allisonmb/game-gear/A-Z80/docs/png/a-z80-toplevel.png

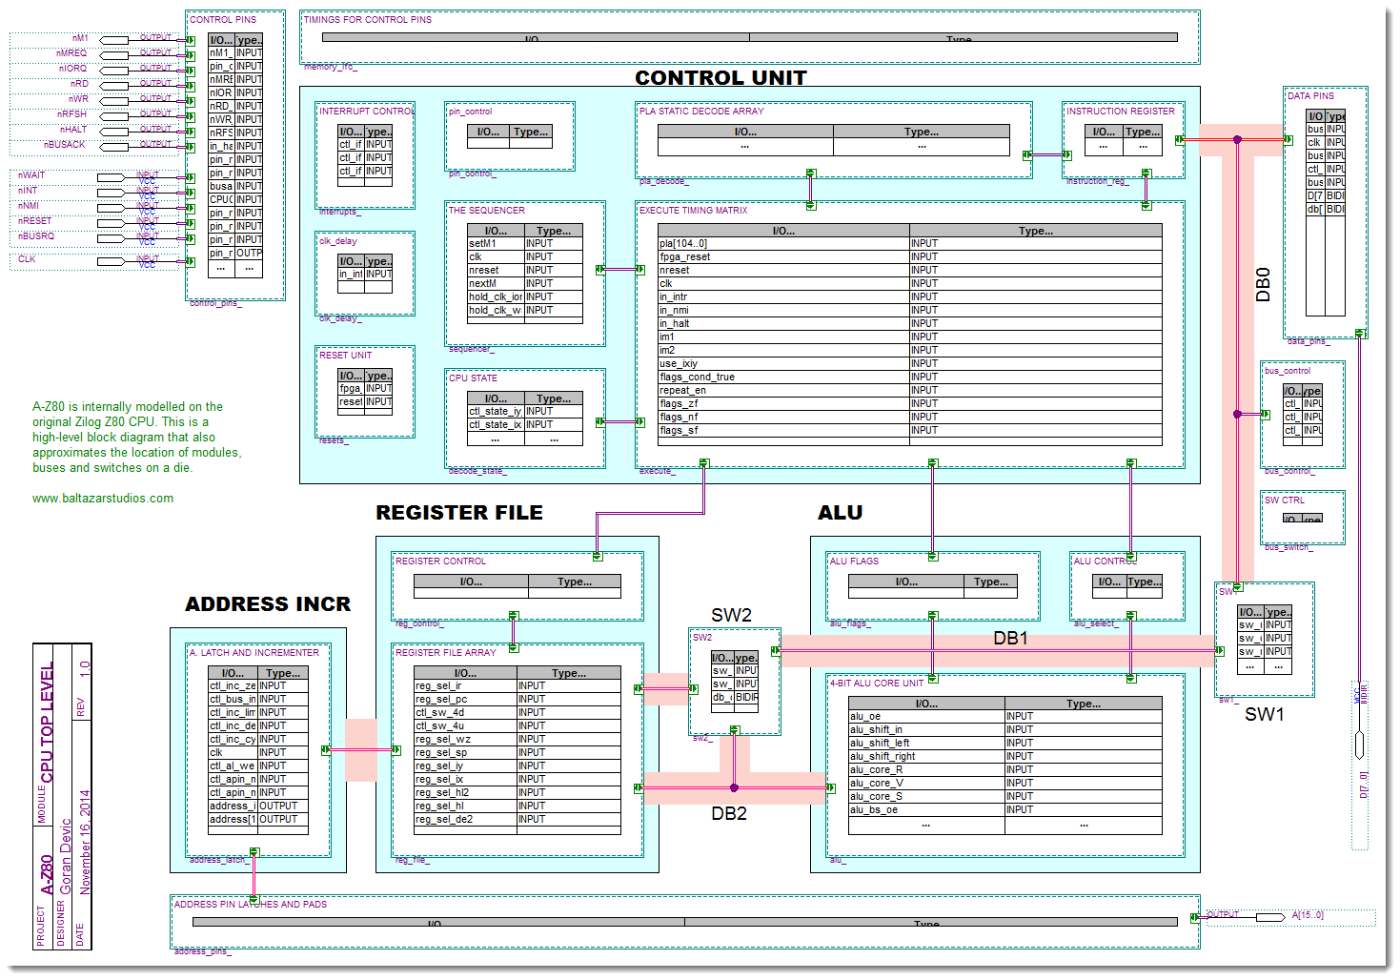
A-Z80/docs/png/a-z80-toplevel.png
