allisonmb/game-gear/A-Z80/docs/png/z80-address_pins.png

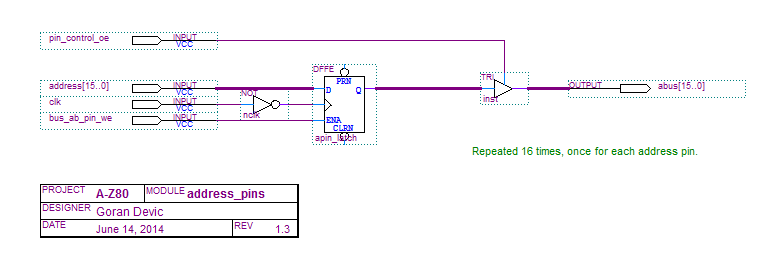
A-Z80/docs/png/z80-address_pins.png
