allisonmb/game-gear/A-Z80/docs/png/z80-alu.png

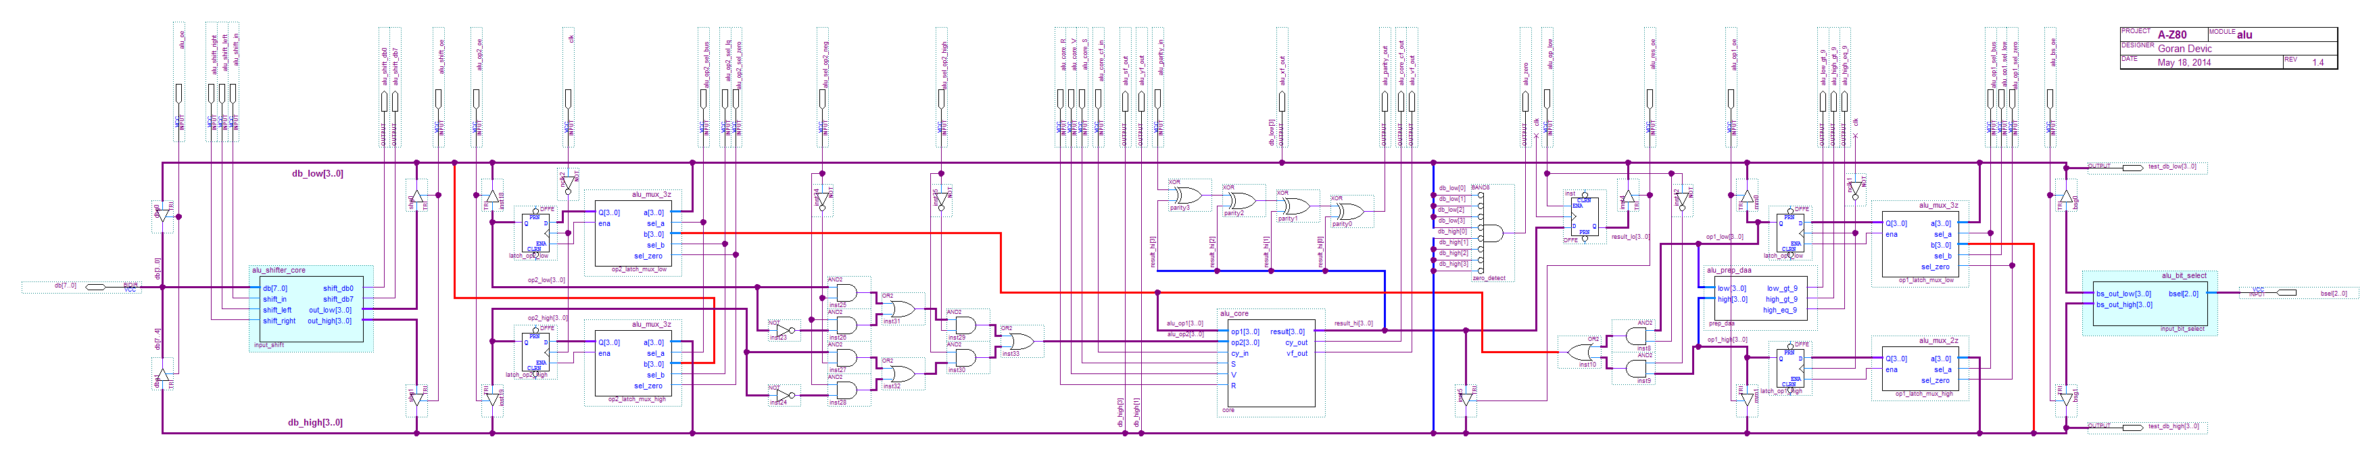
A-Z80/docs/png/z80-alu.png
