allisonmb/game-gear/A-Z80/docs/png/z80-alu_control.png

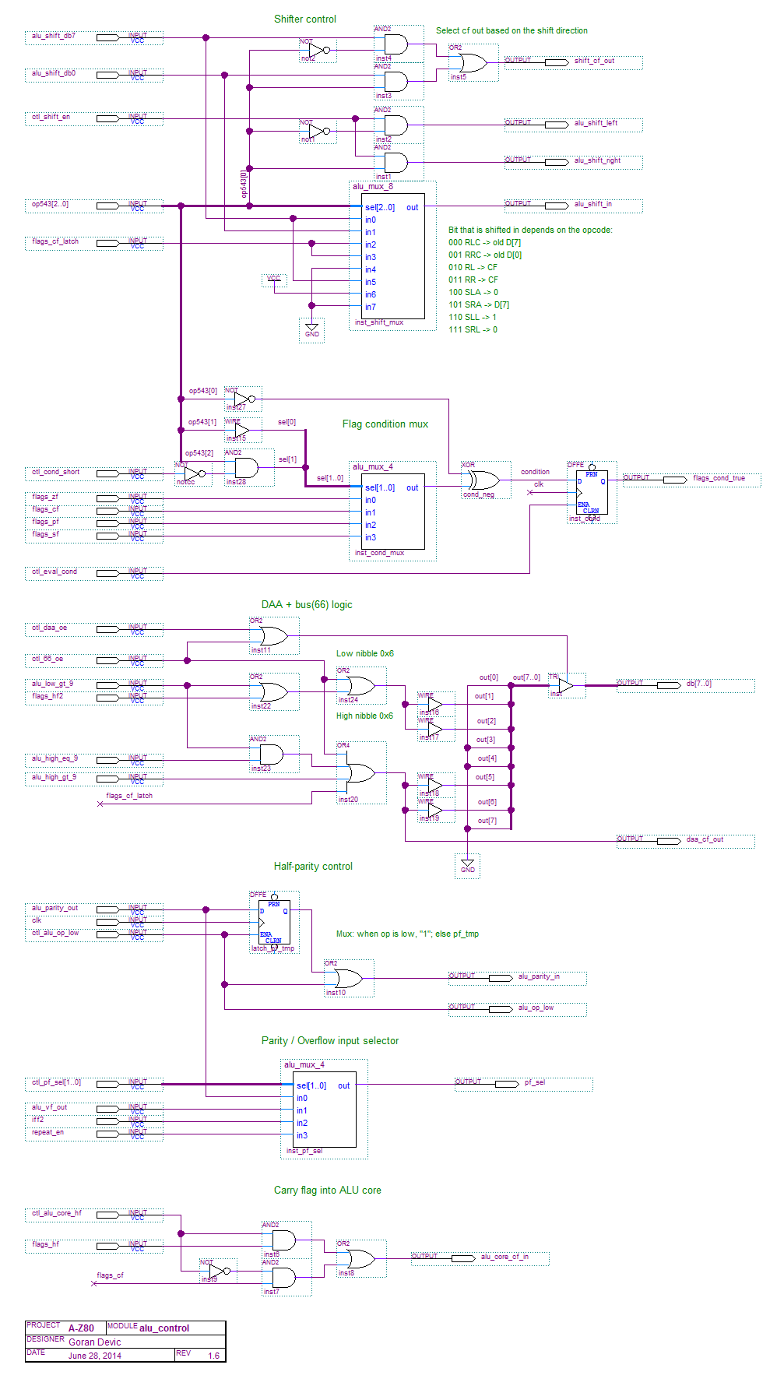
A-Z80/docs/png/z80-alu_control.png
