allisonmb/game-gear/A-Z80/docs/png/z80-alu_flags.png

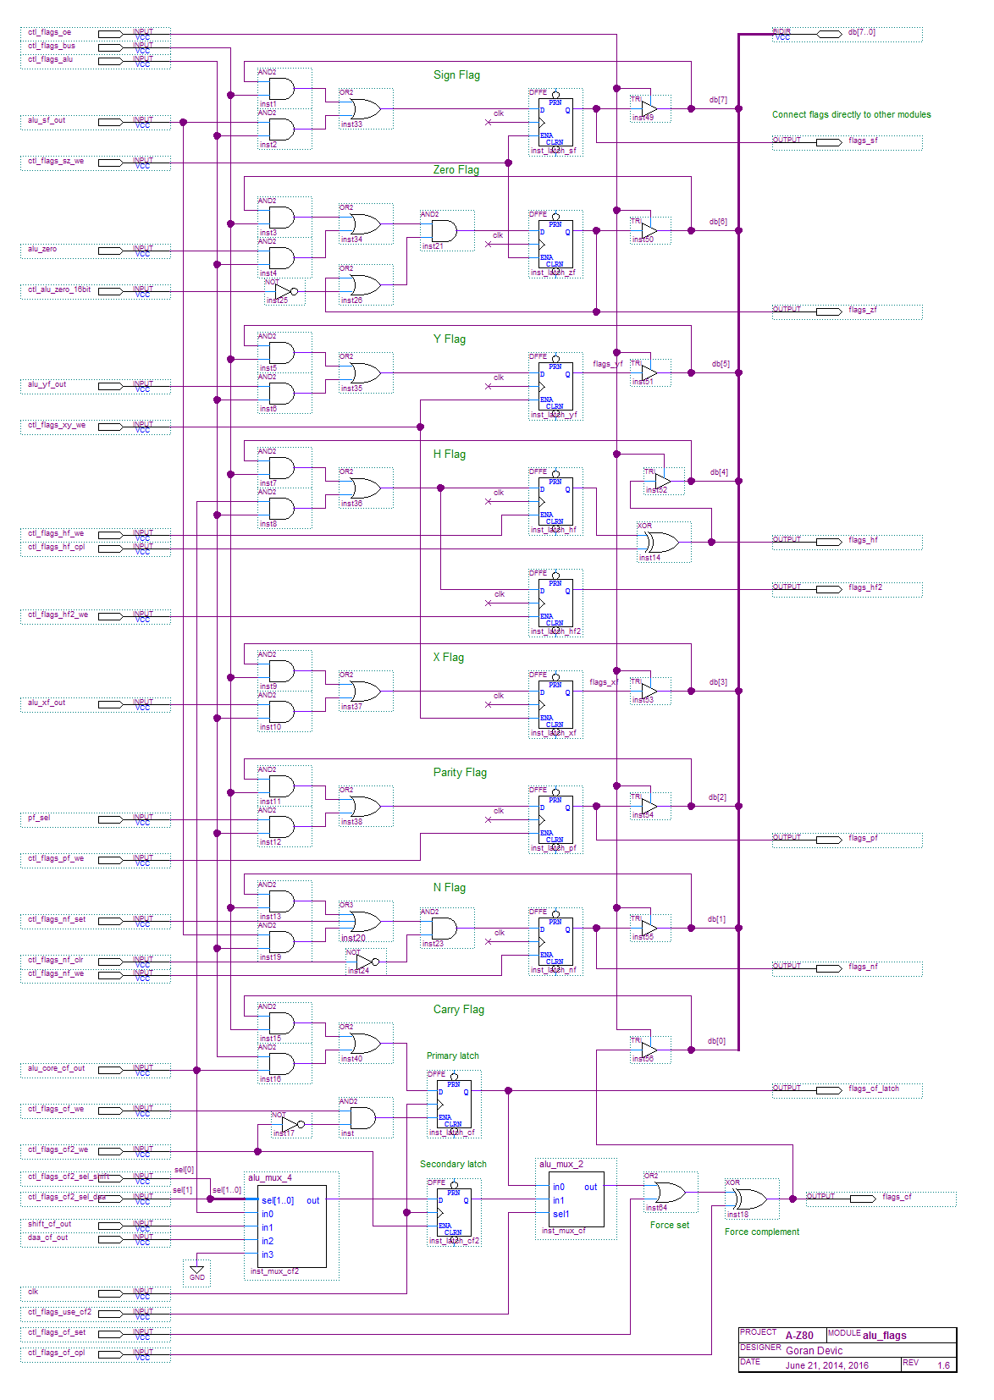
A-Z80/docs/png/z80-alu_flags.png
