allisonmb/game-gear/A-Z80/docs/png/z80-alu_mux_2z.png

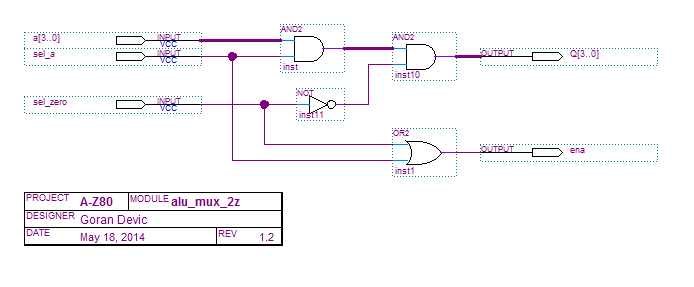
A-Z80/docs/png/z80-alu_mux_2z.png
