allisonmb/game-gear/A-Z80/docs/png/z80-alu_mux_4.png

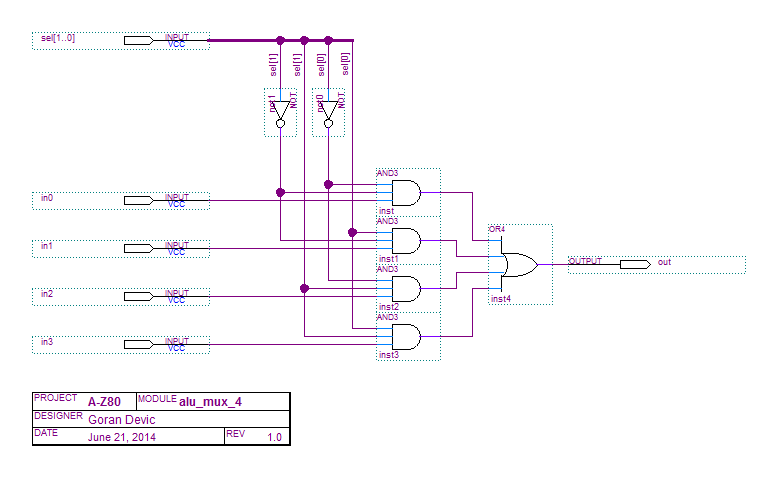
A-Z80/docs/png/z80-alu_mux_4.png
