allisonmb/game-gear/A-Z80/docs/png/z80-alu_prep_daa.png

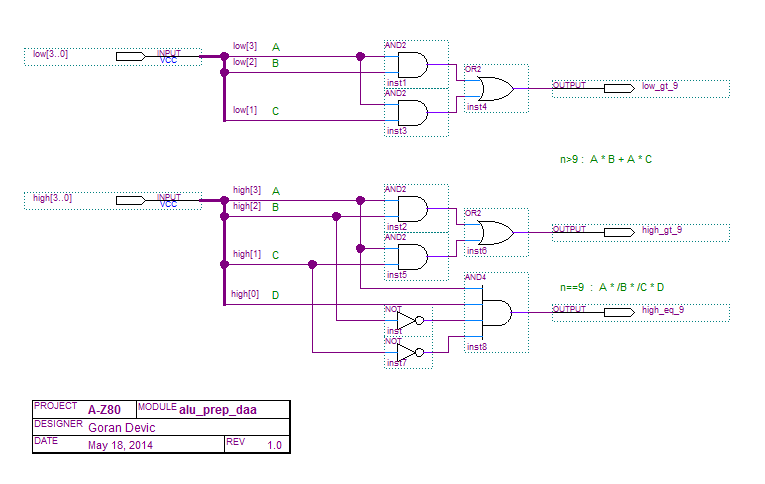
A-Z80/docs/png/z80-alu_prep_daa.png
