allisonmb/game-gear/A-Z80/docs/png/z80-alu_select.png

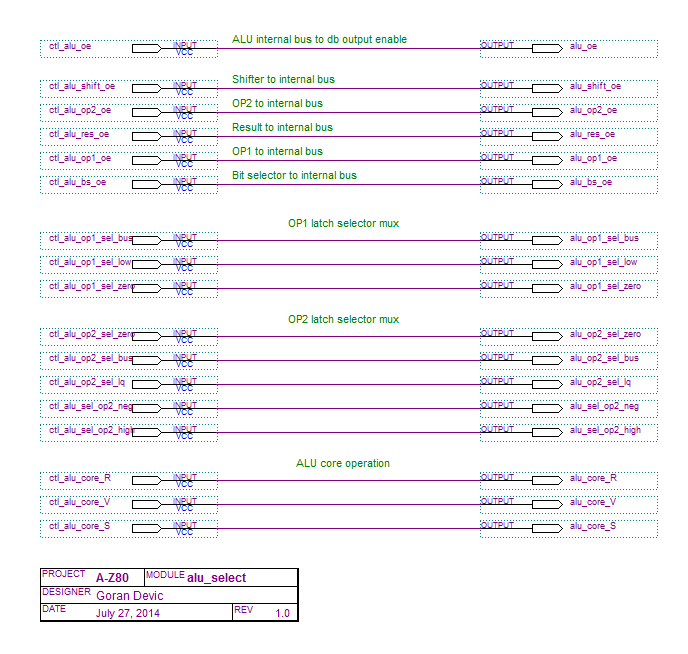
A-Z80/docs/png/z80-alu_select.png
