allisonmb/game-gear/A-Z80/docs/png/z80-clk_delay.png

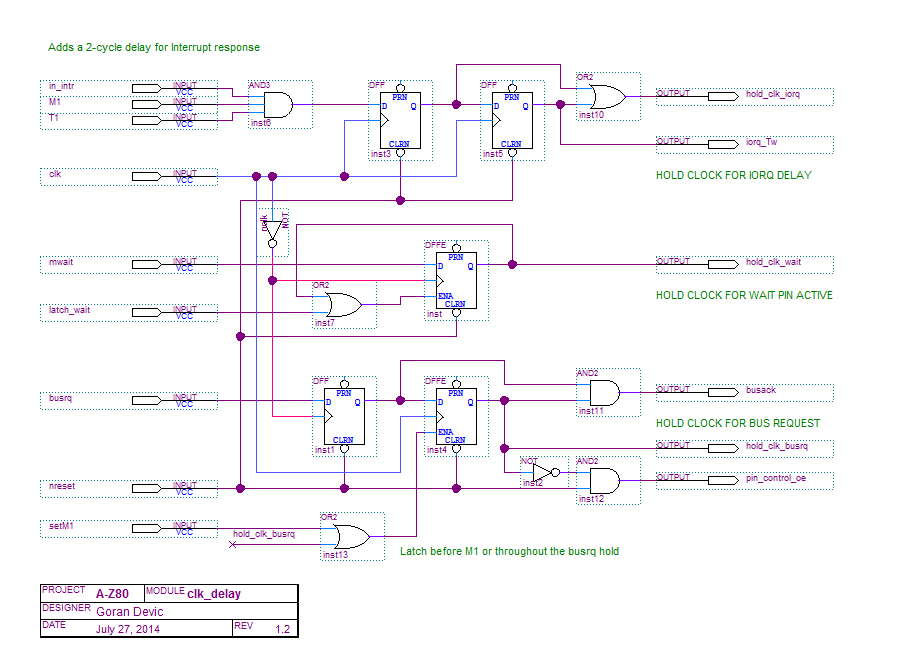
A-Z80/docs/png/z80-clk_delay.png
