allisonmb/game-gear/A-Z80/docs/png/z80-control_pins_n.png

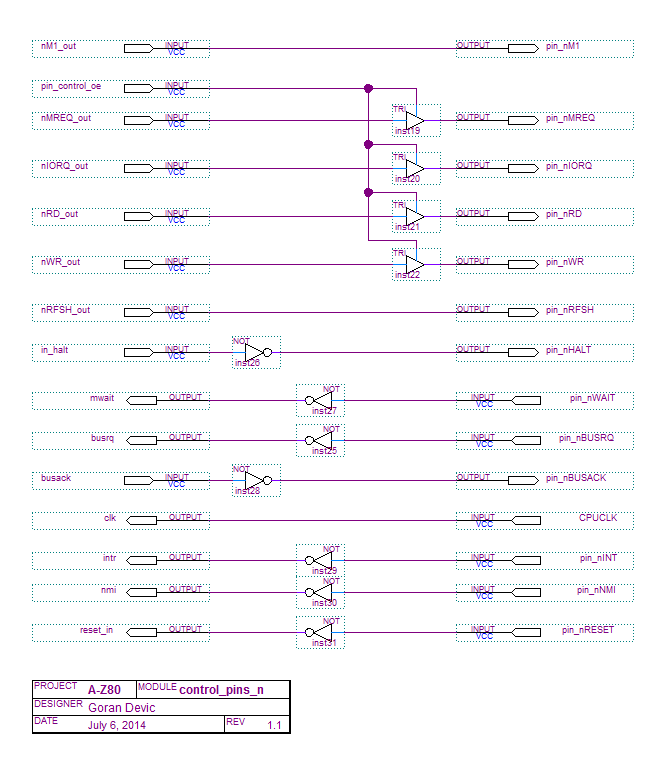
A-Z80/docs/png/z80-control_pins_n.png
