allisonmb/game-gear/A-Z80/docs/png/z80-data_pins.png

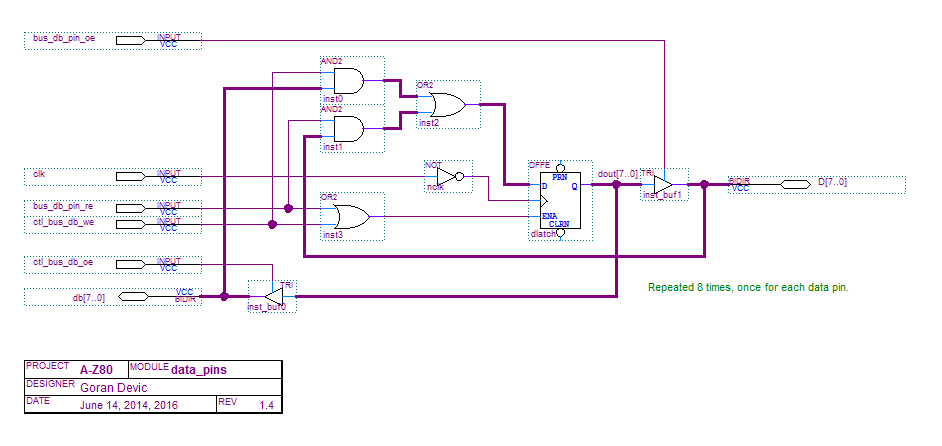
A-Z80/docs/png/z80-data_pins.png
