allisonmb/game-gear/A-Z80/docs/png/z80-data_switch.png

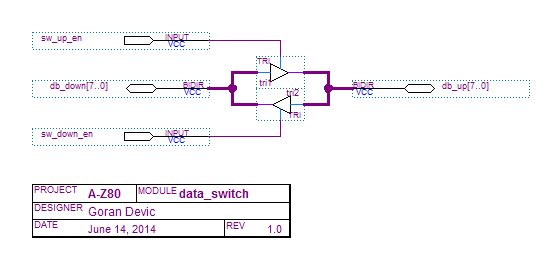
A-Z80/docs/png/z80-data_switch.png
