allisonmb/game-gear/A-Z80/docs/png/z80-data_switch_mask.png

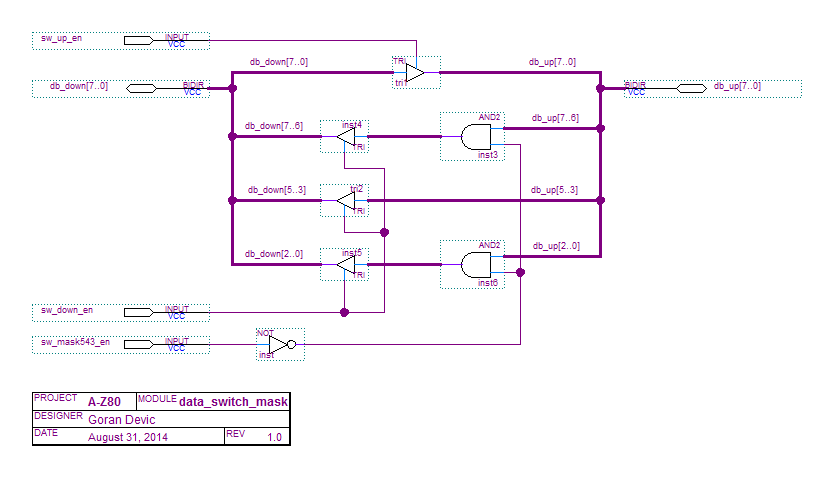
A-Z80/docs/png/z80-data_switch_mask.png
