allisonmb/game-gear/A-Z80/docs/png/z80-decode_state.png

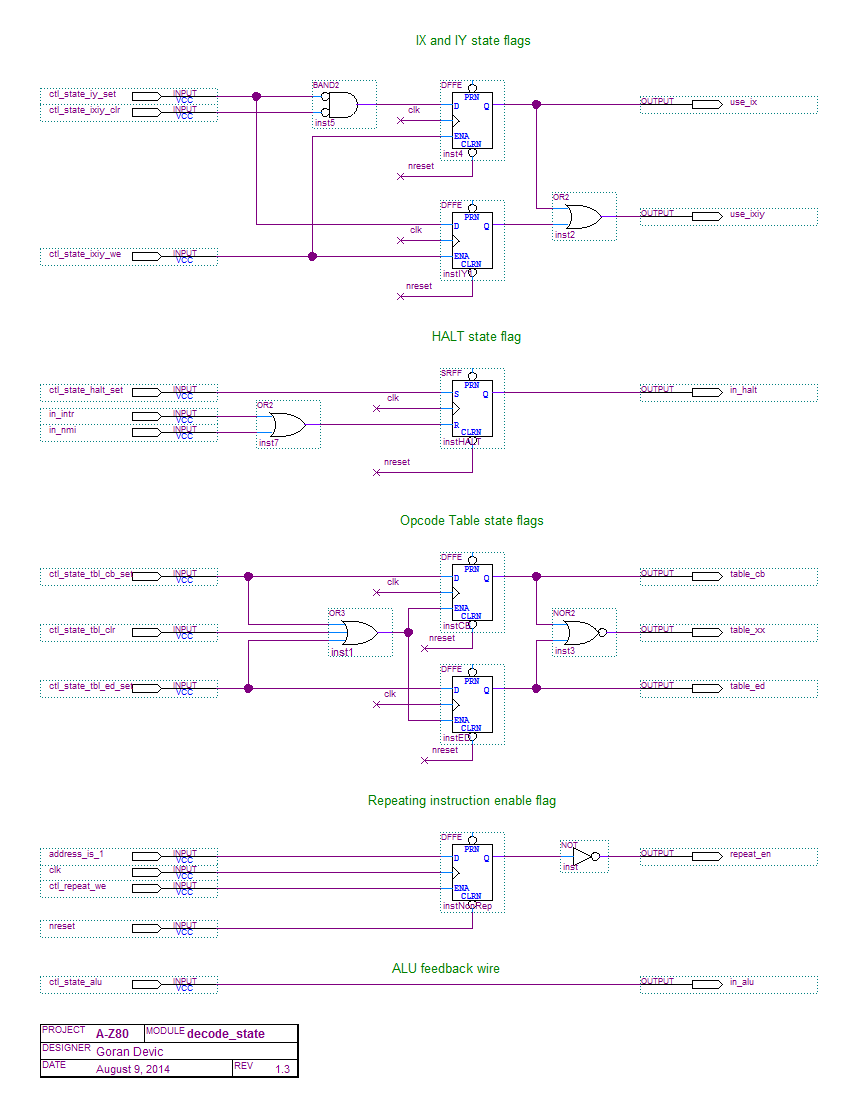
A-Z80/docs/png/z80-decode_state.png
