allisonmb/game-gear/A-Z80/docs/png/z80-inc_dec.png

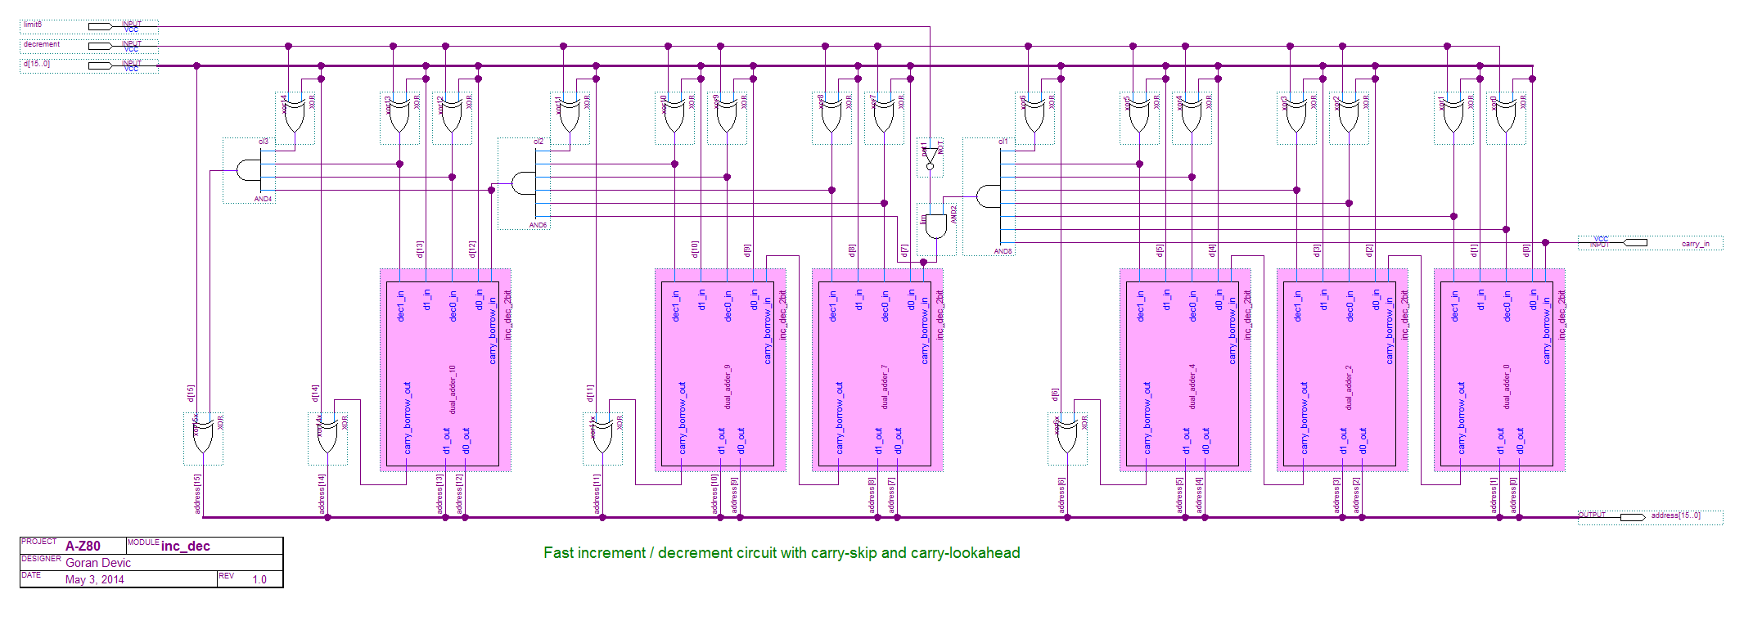
A-Z80/docs/png/z80-inc_dec.png
