allisonmb/game-gear/A-Z80/docs/png/z80-interrupts.png

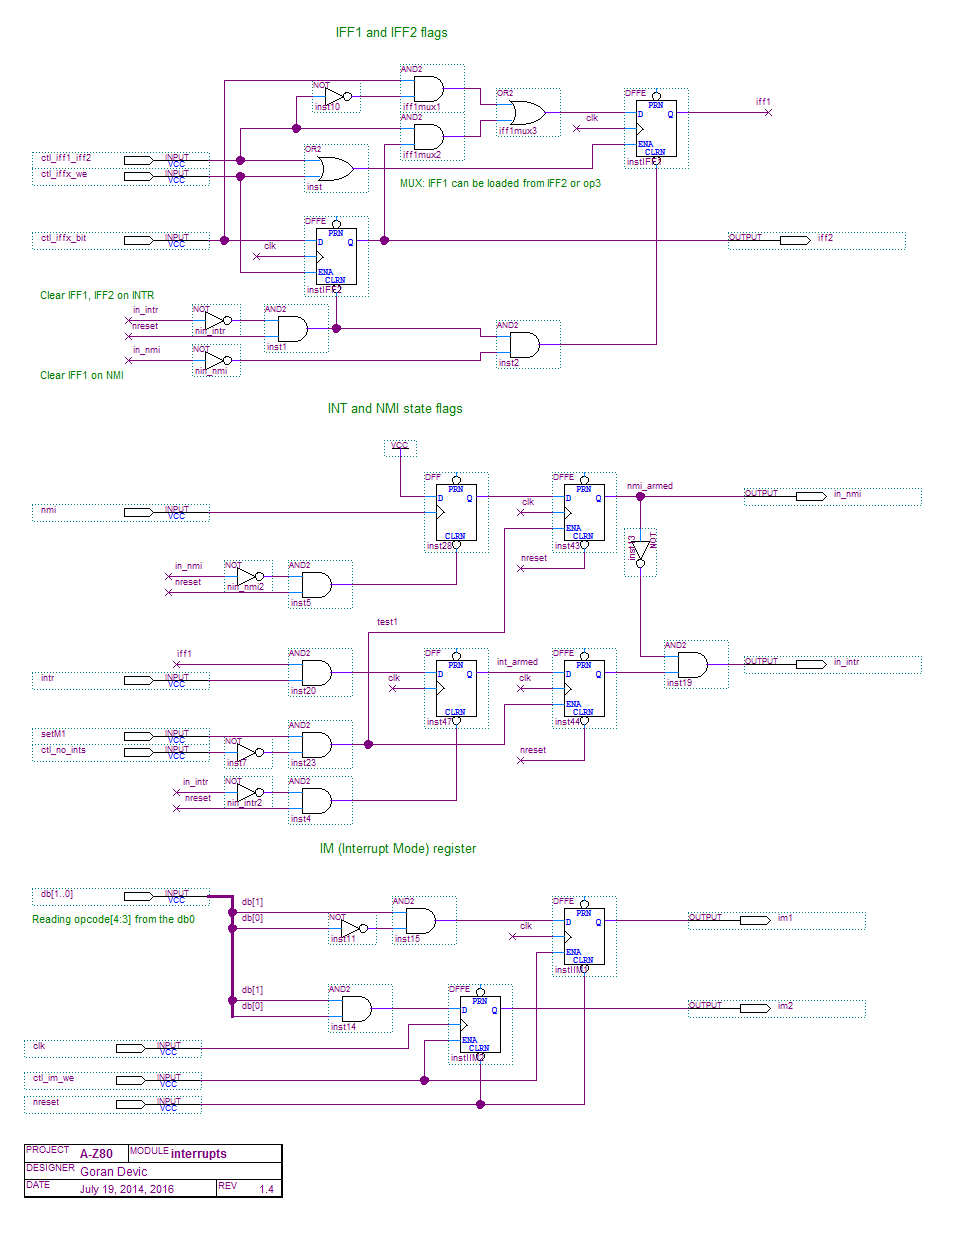
A-Z80/docs/png/z80-interrupts.png
