allisonmb/game-gear/A-Z80/docs/png/z80-ir.png

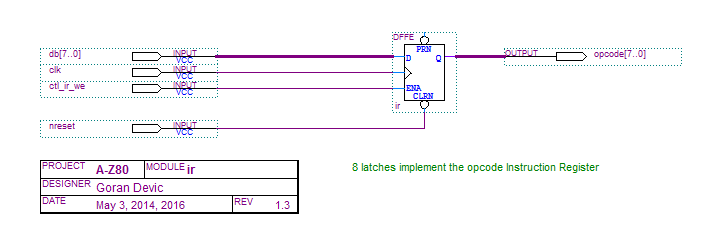
A-Z80/docs/png/z80-ir.png
