allisonmb/game-gear/A-Z80/docs/png/z80-memory_ifc.png

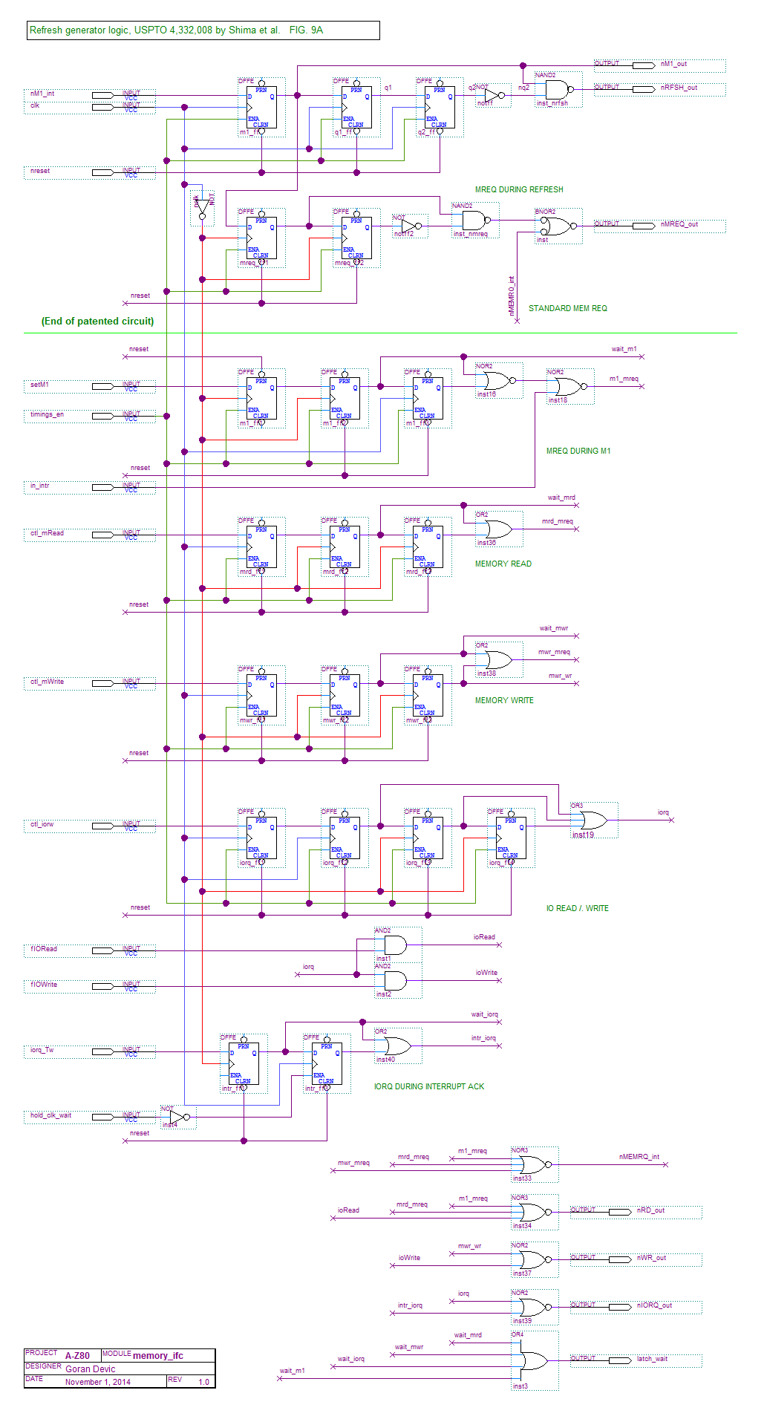
A-Z80/docs/png/z80-memory_ifc.png
