allisonmb/game-gear/A-Z80/docs/png/z80-pin_control.png

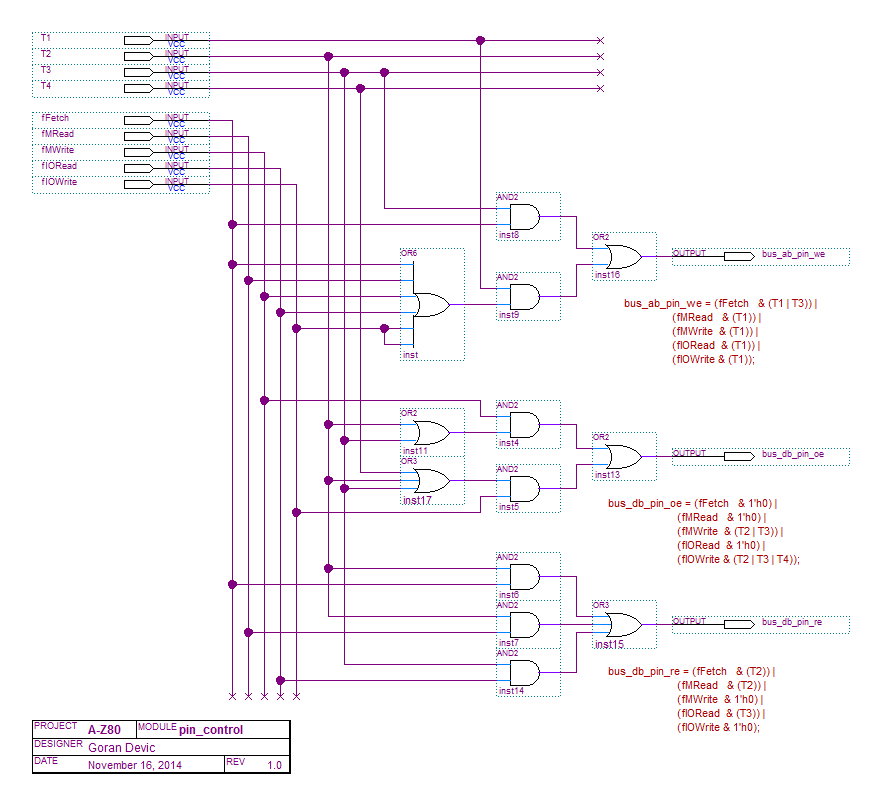
A-Z80/docs/png/z80-pin_control.png
