allisonmb/game-gear/A-Z80/docs/png/z80-reg_control.png

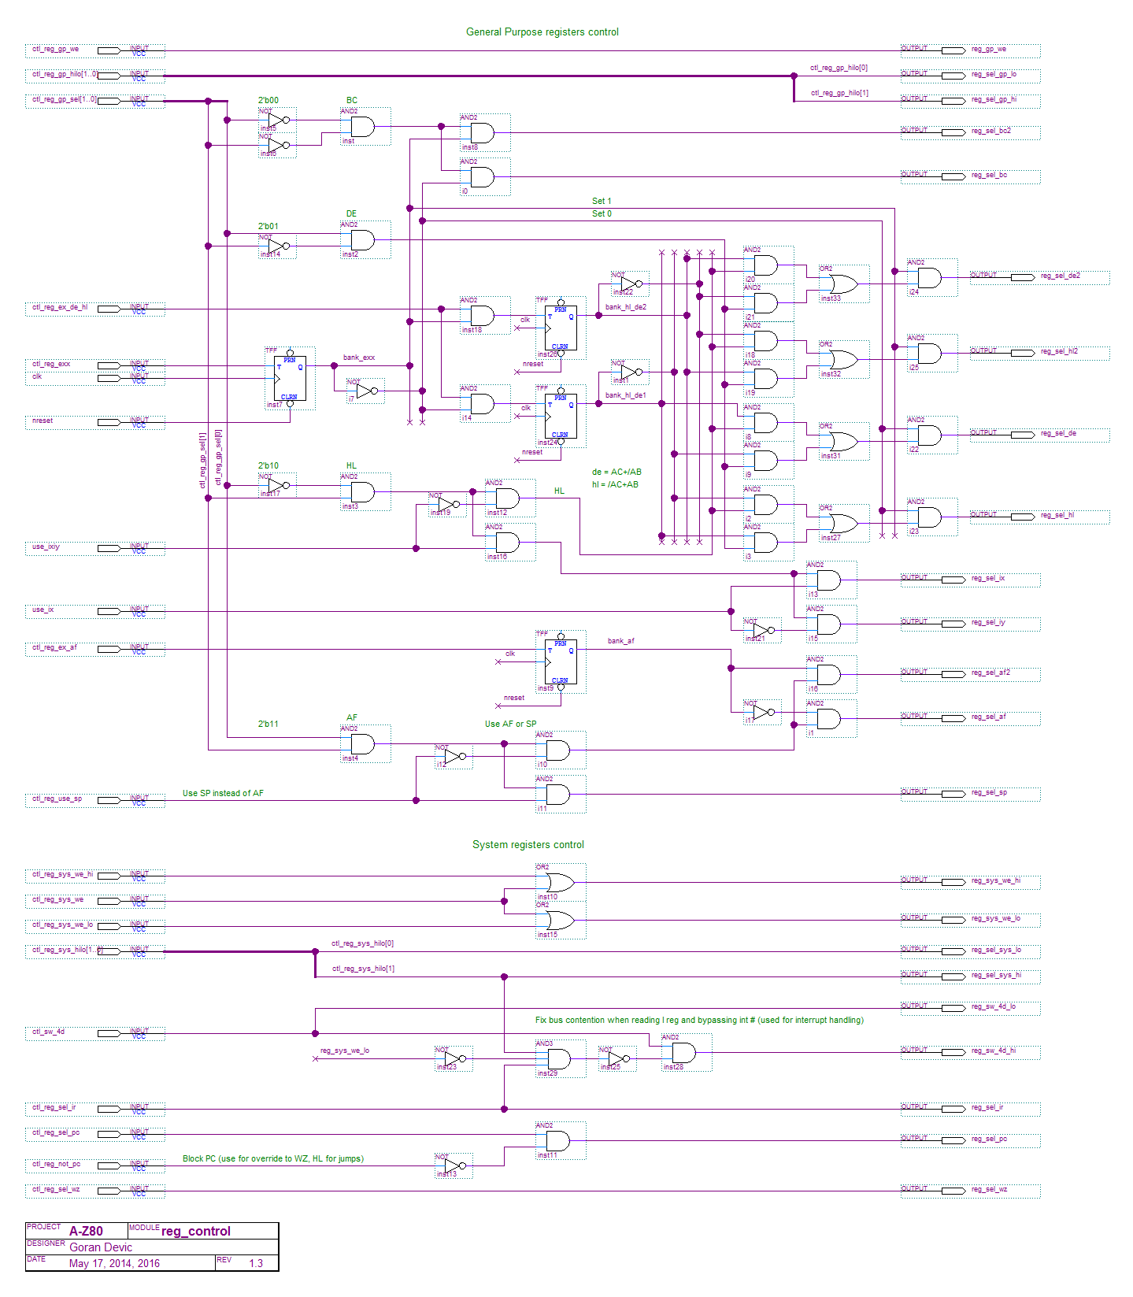
A-Z80/docs/png/z80-reg_control.png
