allisonmb/game-gear/A-Z80/docs/png/z80-resets.png

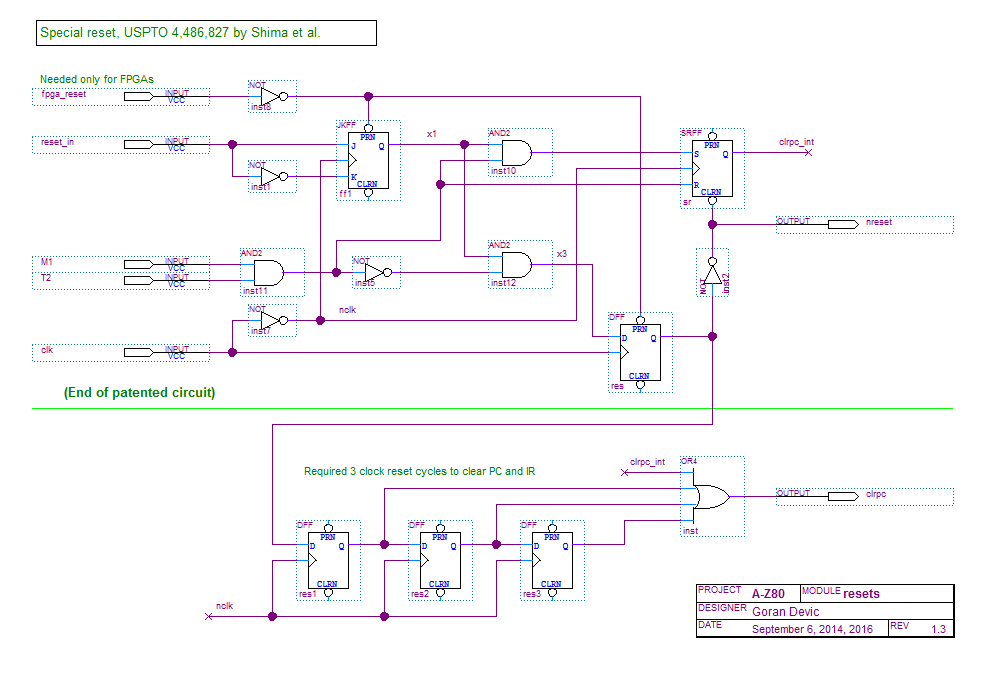
A-Z80/docs/png/z80-resets.png
