allisonmb/game-gear/A-Z80/docs/png/z80-sequencer.png

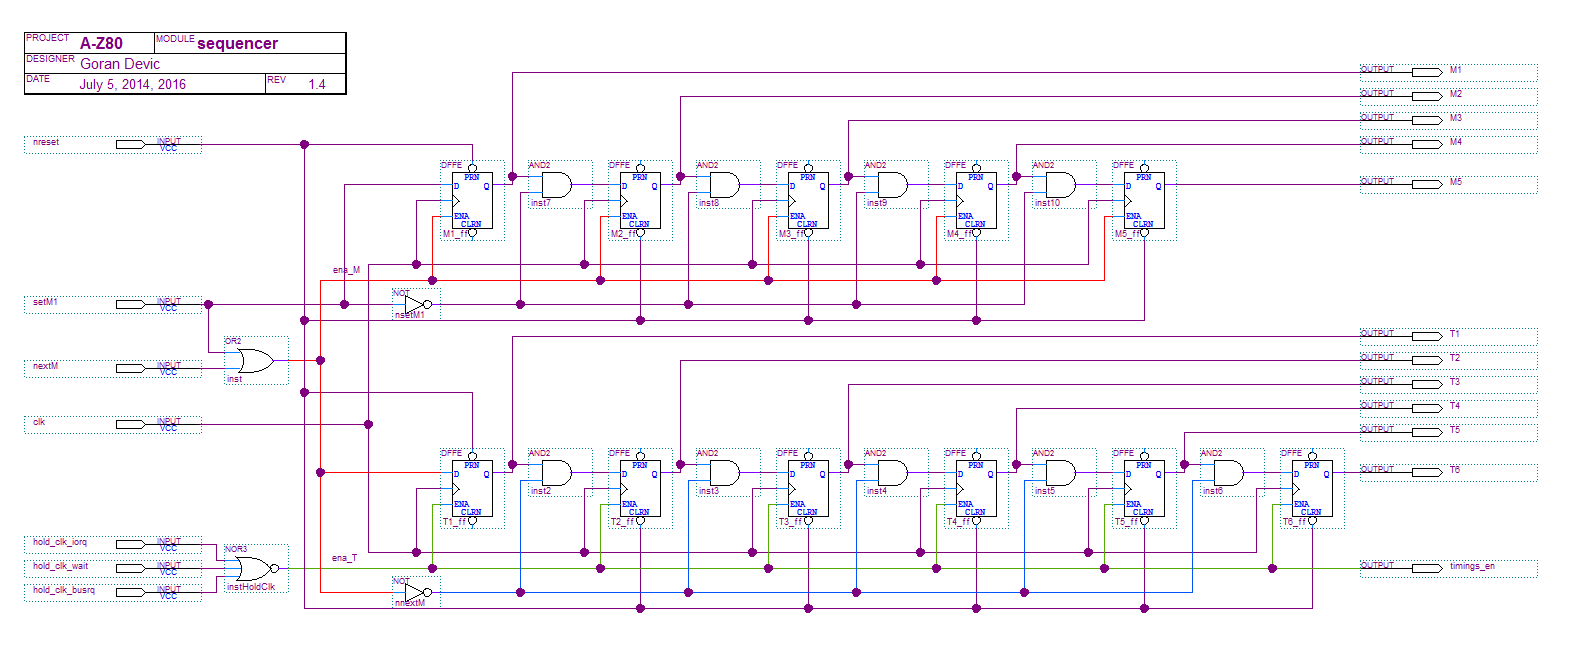
A-Z80/docs/png/z80-sequencer.png
