allisonmb/game-gear/A-Z80/docs/pdf/clk_delay.pdf

### Adds a 2-cycle delay for Interrupt response

### HOLD CLOCK FOR IORQ DELAY

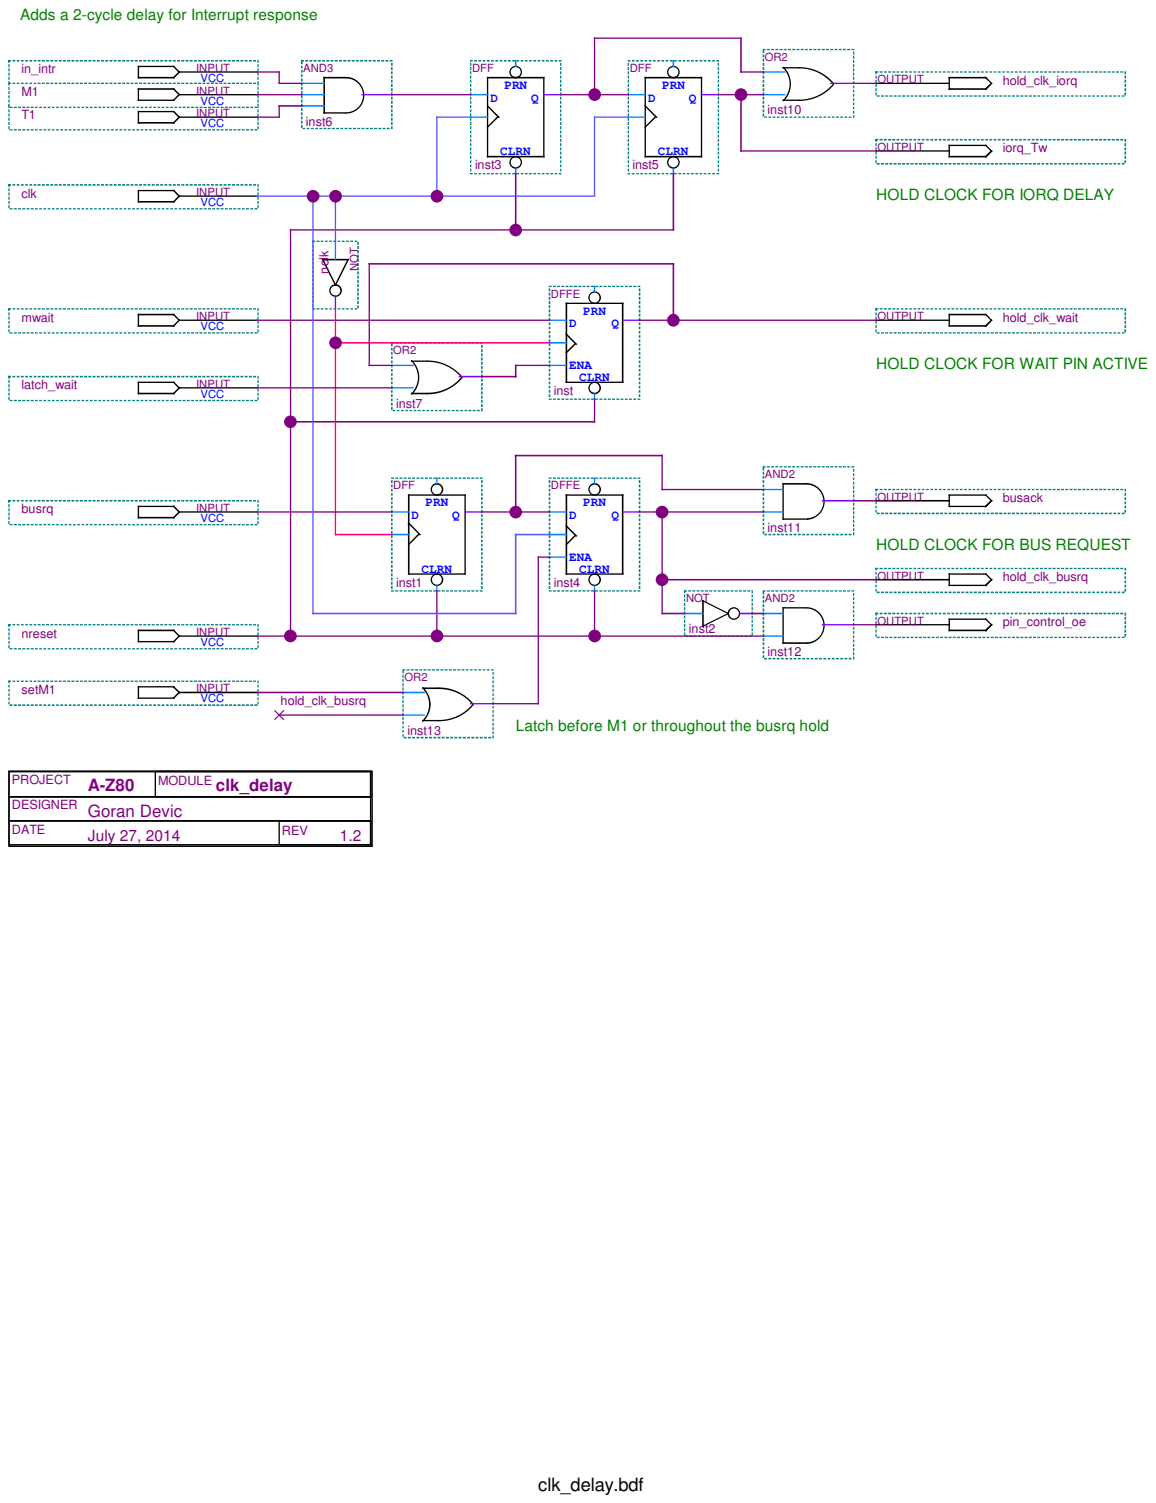
[picture p74: page 1]
clk_delay.bdf; hold_clk_busrq; VCC; clk; INPUT; in_intr; nreset; latch_wait; mwait; busrq; setM1; OUTPUT; hold_clk_iorq; hold_clk_wait; iorq_Tw; busack; pin_control_oe; CLRN; PRN; DFF; inst3; inst5; inst10; ENA; DFFE; inst; AND3; inst6; inst7; nclk; NOT; AND2; inst11; inst2; inst12; inst4; inst13; inst1; PROJECT; MODULE clk_delay; DATE; July 27, 2014; REV

HOLD CLOCK FOR WAIT PIN ACTIVE

HOLD CLOCK FOR BUS REQUEST

Latch before M1 or throughout the busrq hold

DESIGNER Goran Devic
