allisonmb/game-gear/A-Z80/docs/pdf/interrupts.pdf

## IFF1 and IFF2 flags

## MUX: IFF1 can be loaded from IFF2 or op3

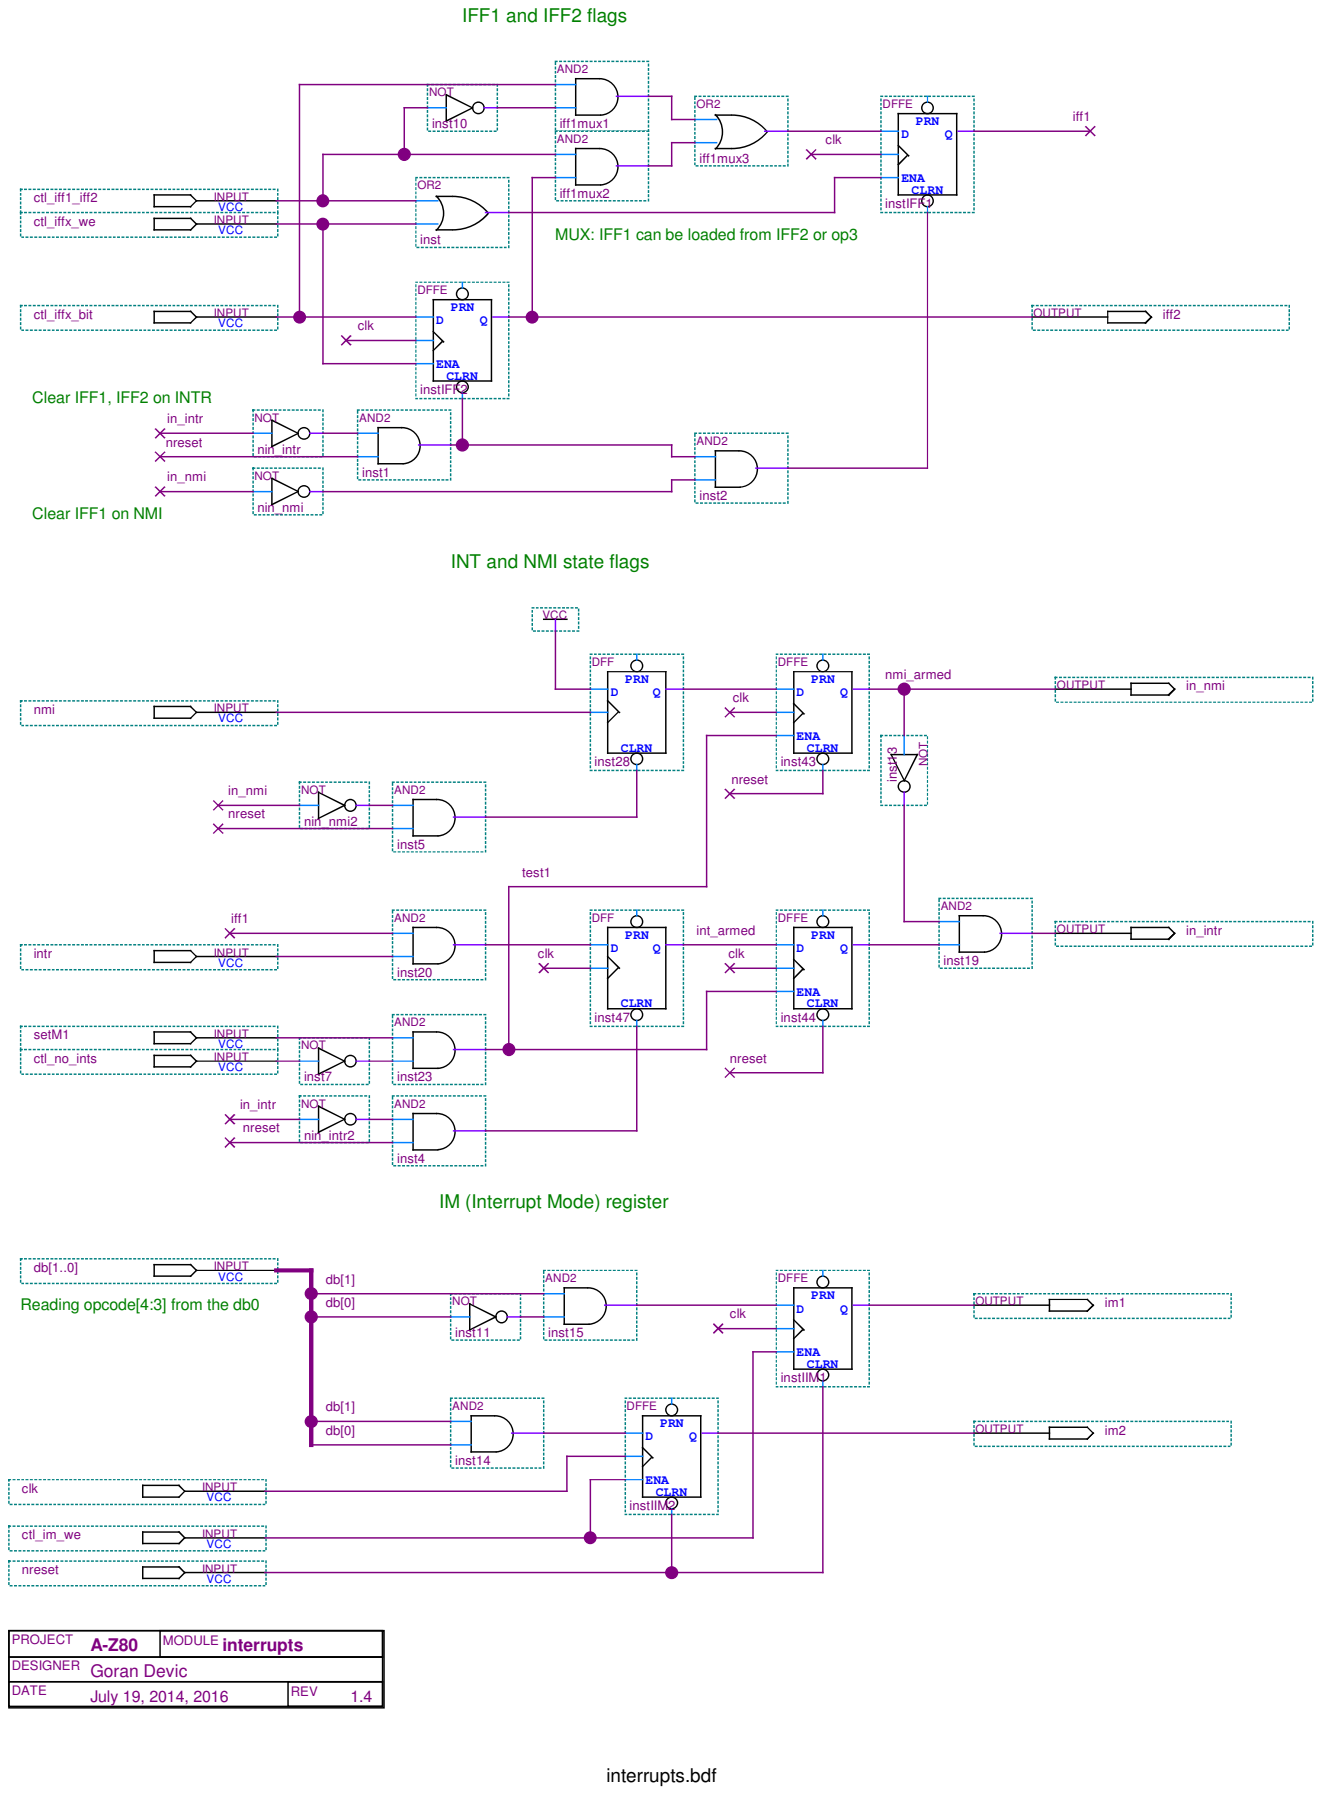
[picture p75: page 1]
interrupts.bdf; iff1; clk; in_intr; nreset; in_nmi; test1; nmi_armed; int_armed; VCC ctl_iff1_iff2; INPUT; VCC nmi; VCC setM1; VCC; intr; ctl_iffx_we; ctl_iffx_bit; ctl_im_we; VCC clk; ctl_no_ints; OUTPUT; iff2; AND2; inst14; inst15; inst19; inst20; NOT; inst13; inst11; inst; inst7; inst23; CLRN; PRN; DFF; inst28; ENA; DFFE; inst43; inst44; inst47; instIIM1; instIIM2; instIFF1; instIFF2; iff1mux1 AND2; iff1mux2; iff1mux3; inst10; inst1; nin_intr; nin_nmi; inst2; inst4; nin_intr2; inst5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

Clear IFF1, IFF2 on INTR

Clear IFF1 on NMI

INT and NMI state flags

IM (Interrupt Mode) register

Reading opcode[4:3] from the db0

DESIGNER Goran Devic
