allisonmb/game-gear/A-Z80/docs/pdf/memory_ifc.pdf

# memory_ifc.bdf nMEMRQ_int

## Refresh generator logic, USPTO 4,332,008 by Shima et al. FIG. 9A

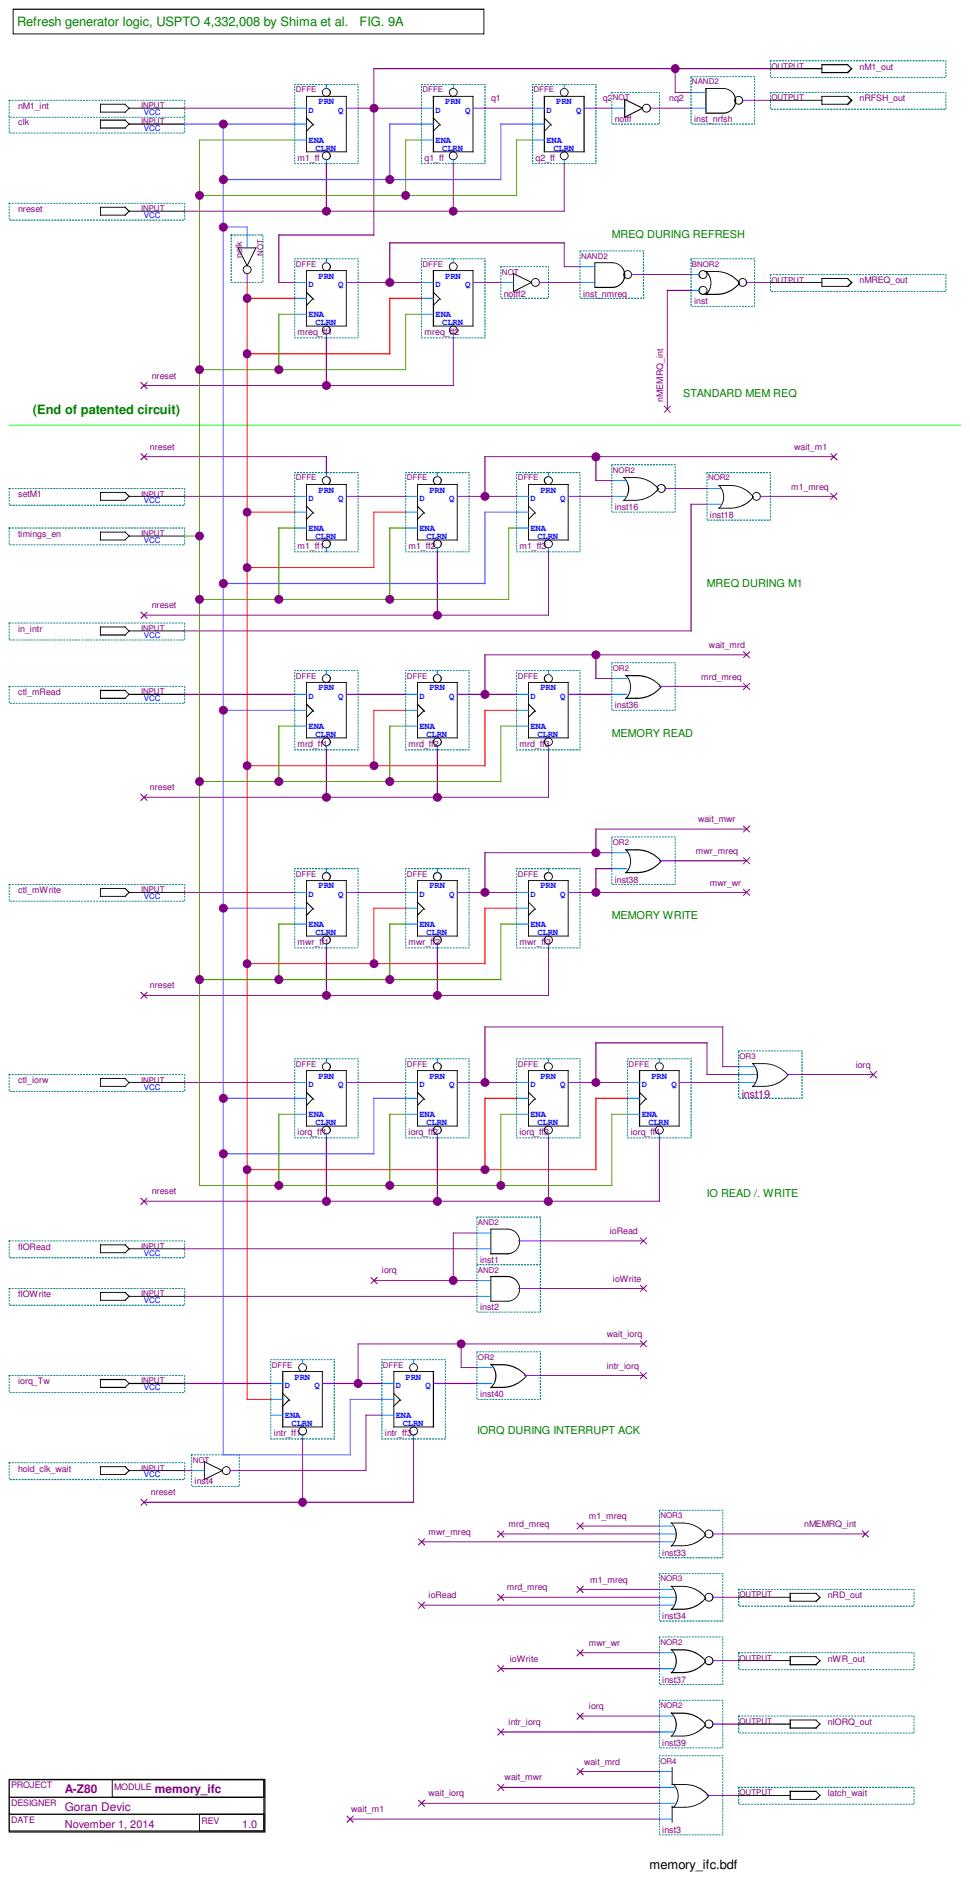
[picture p76: page 1]
nreset; mrd_mreq; iorq; m1_mreq; mwr_wr; mwr_mreq; ioRead; ioWrite; nMEMRQ_int; intr_iorq; wait_m1; wait_mrd; wait_iorq; wait_mwr; MREQ DURING M1; MEMORY WRITE; MEMORY READ; VCC; clk; INPUT; nM1_int; ctl_mRead; VCC ctl_mWrite; in_intr; VCC nreset; fIORead; VCC fIOWrite; VCC setM1; ctl_iorw; timings_en; iorq_Tw; VCC hold_clk_wait; OUTPUT; nM1_out; nRFSH_out; nMREQ_out; nRD_out; nWR_out; nIORQ_out; latch_wait; NOT; notff; NAND2; inst_nrfsh; nclk; notff2; inst_nmreq; BNOR2; inst; inst19; NOR2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

MREQ DURING REFRESH

STANDARD MEM REQ

(End of patented circuit)

IO READ /. WRITE

IORQ DURING INTERRUPT ACK

DESIGNER Goran Devic
