allisonmb/game-gear/A-Z80/docs/pdf/alu_flags.pdf

### Connect flags directly to other modules

## Zero Flag

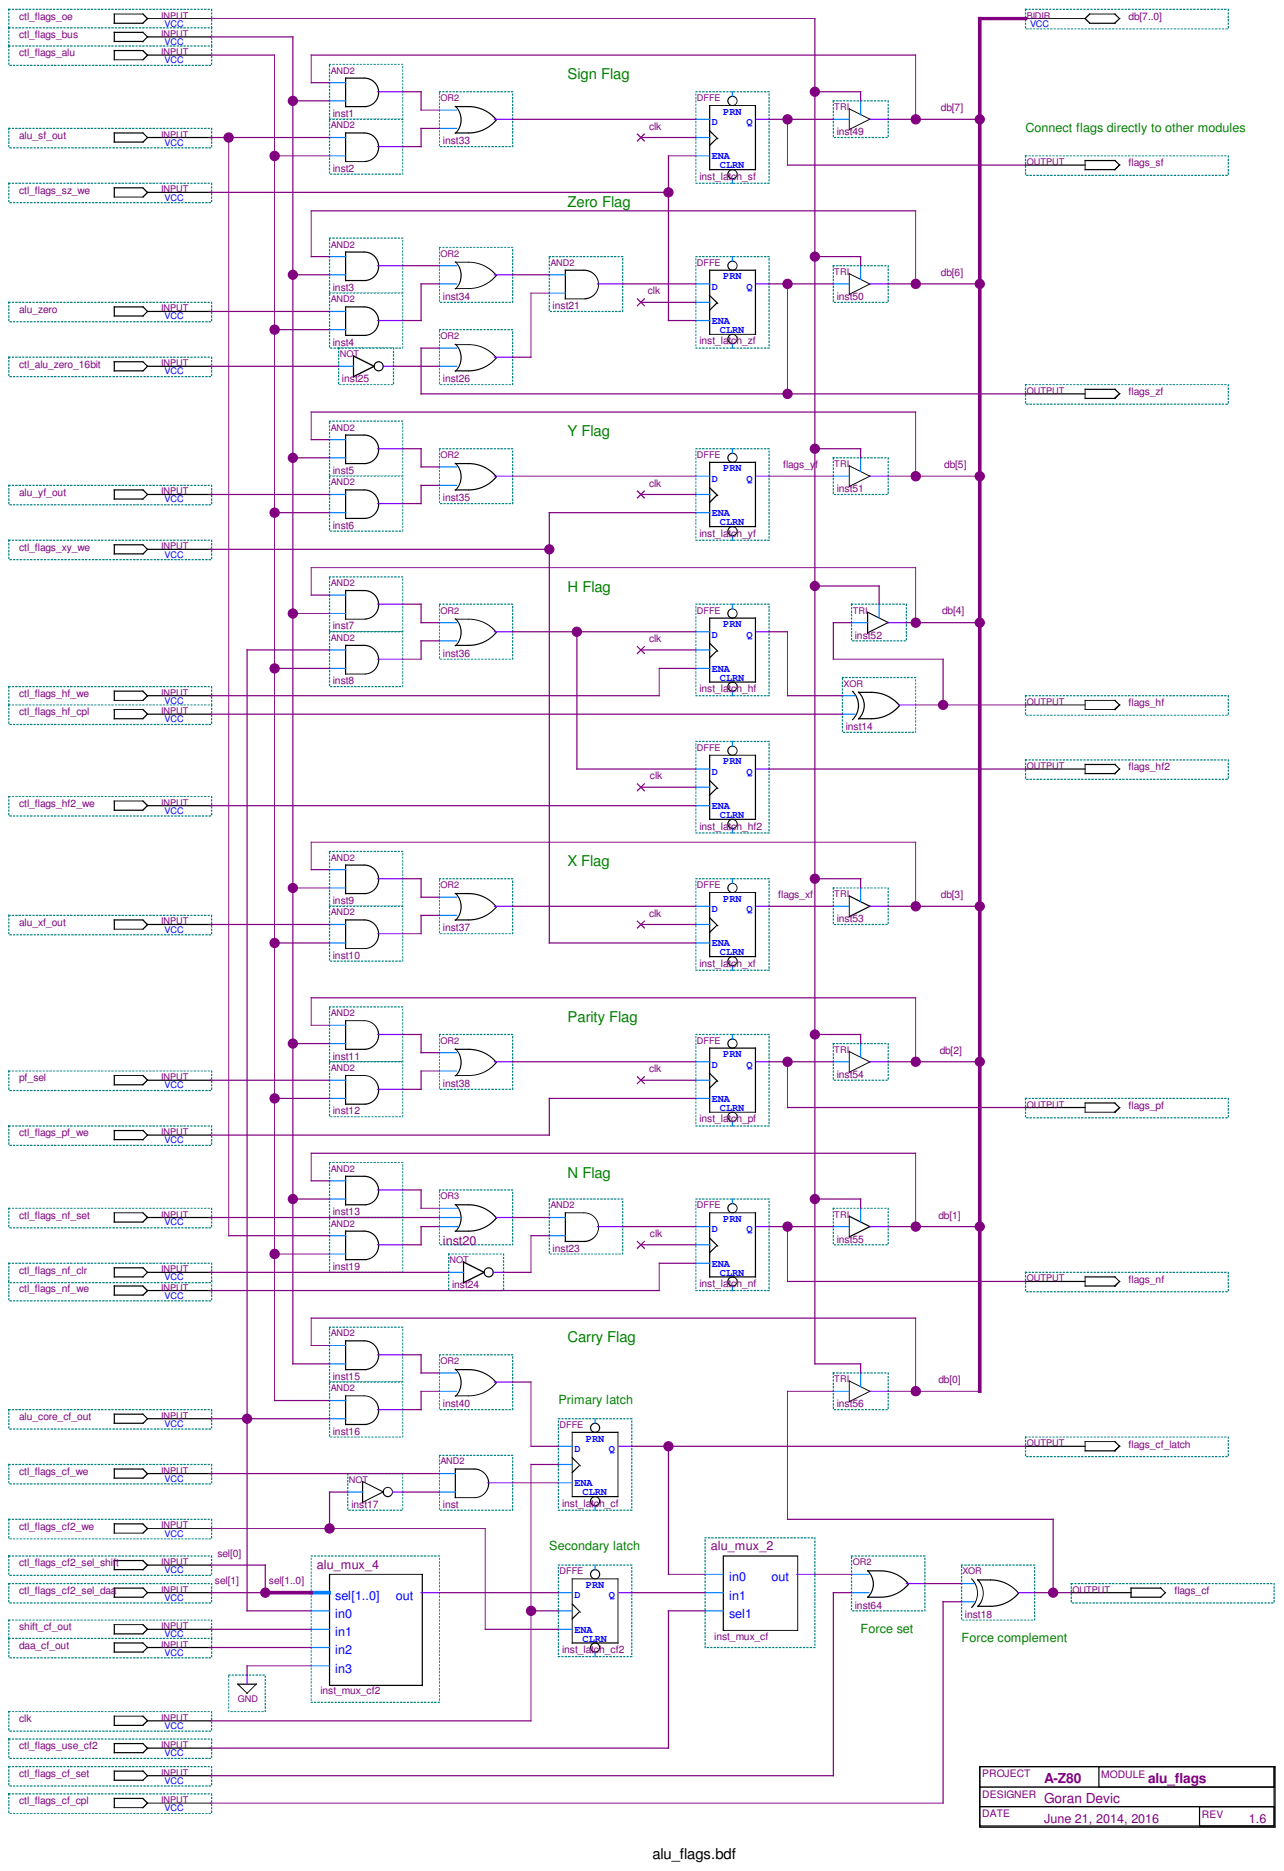
[picture p83: page 1]
alu_flags.bdf; flags_yf; flags_xf; clk; sel[0]; sel[1]; sel[1..0]; Carry Flag; Parity Flag; N Flag; Sign Flag; Y Flag; X Flag; H Flag; Force set; Force complement; Primary latch; Secondary latch; VCC; ctl_flags_oe; INPUT; VCC ctl_flags_bus; ctl_flags_alu; alu_sf_out; VCC alu_yf_out; alu_xf_out; VCC ctl_flags_nf_set; VCC alu_zero; shift_cf_out; alu_core_cf_out; daa_cf_out; VCC ctl_flags_cf_set; ctl_flags_cf_cpl; VCC pf_sel; ctl_flags_cf_we; ctl_flags_sz_we; ctl_flags_xy_we; ctl_flags_hf_we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

DESIGNER Goran Devic
