allisonmb/game-gear/A-Z80/docs/pdf/alu_select.pdf

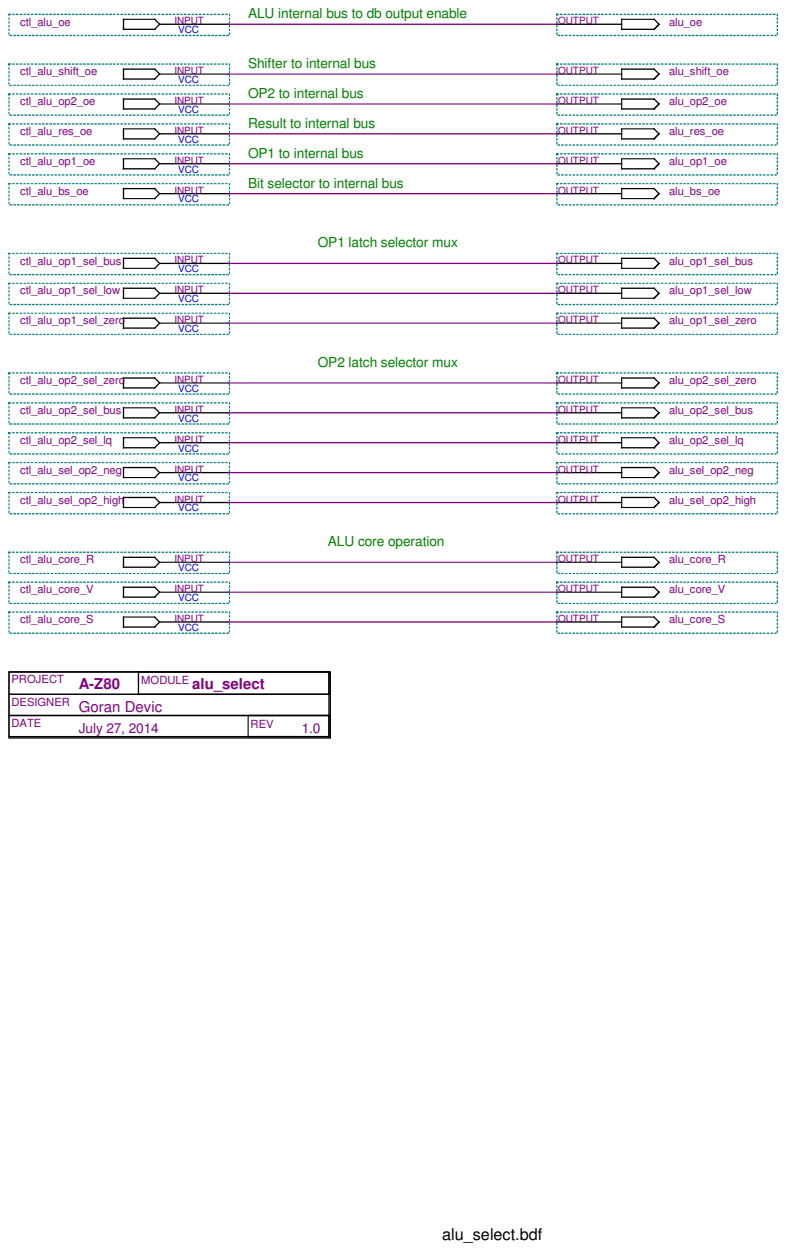
[picture p84: page 1]
alu_select.bdf; VCC; ctl_alu_oe; INPUT; ctl_alu_shift_oe; ctl_alu_op2_oe; ctl_alu_res_oe; ctl_alu_op1_oe; ctl_alu_bs_oe; ctl_alu_op1_sel_bus; ctl_alu_op1_sel_low; ctl_alu_op1_sel_zero; ctl_alu_op2_sel_zero; ctl_alu_op2_sel_bus; ctl_alu_op2_sel_lq; ctl_alu_sel_op2_neg; ctl_alu_sel_op2_high; ctl_alu_core_R; ctl_alu_core_V; ctl_alu_core_S; OUTPUT; alu_oe; alu_shift_oe; alu_op2_oe; alu_res_oe; alu_op1_oe; alu_bs_oe; alu_op1_sel_bus; alu_op1_sel_low; alu_op1_sel_zero; alu_op2_sel_zero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

ALU internal bus to db output enable

Shifter to internal bus

OP2 to internal bus

Result to internal bus

OP1 to internal bus

Bit selector to internal bus

OP1 latch selector mux

OP2 latch selector mux

ALU core operation

DESIGNER Goran Devic
