allisonmb/game-gear/A-Z80/docs/pdf/alu_shifter_core.pdf

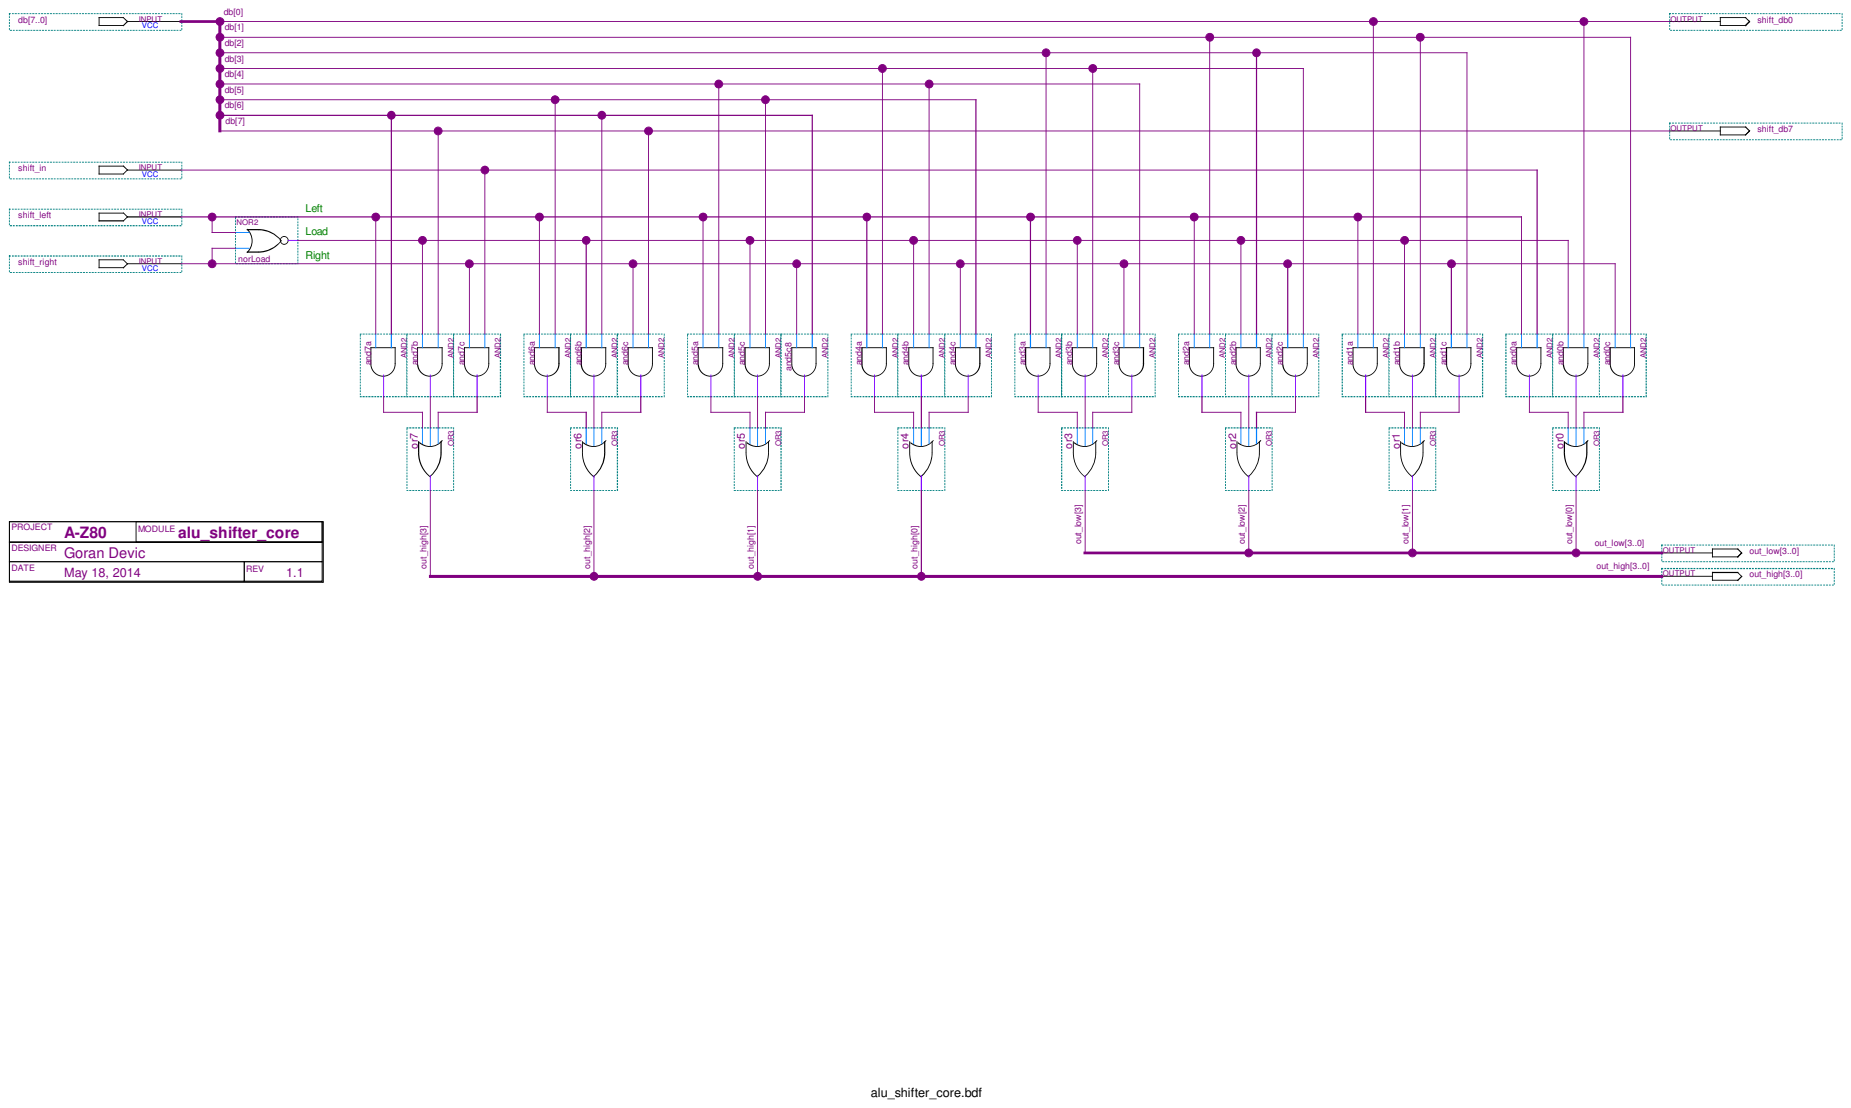
[picture p85: page 1]
alu_shifter_core.bdf; out_high[2]; out_high[1]; out_high[0]; out_low[3]; out_low[2]; out_low[1]; out_low[0]; out_high[3]; out_high[3..0]; out_low[3..0]; Load; Left; Right; VCC shift_in; INPUT; VCC db[7..0]; VCC shift_right; VCC shift_left; OUTPUT; shift_db0; shift_db7; AND2; and5c; and5c8; and7a; and7b; and7c; and6a; and6b; and6c; and5a; and0a; and0b; and0c; and1a; and1b; and1c; and2a; and2b; and2c; and3a; and3b; and3c; and4a; and4b; and4c; NOR2; norLoad; PROJECT; MODULE alu_shifter_core; DATE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

DESIGNER Goran Devic
