allisonmb/game-gear/A-Z80/docs/pdf/control_pins_n.pdf

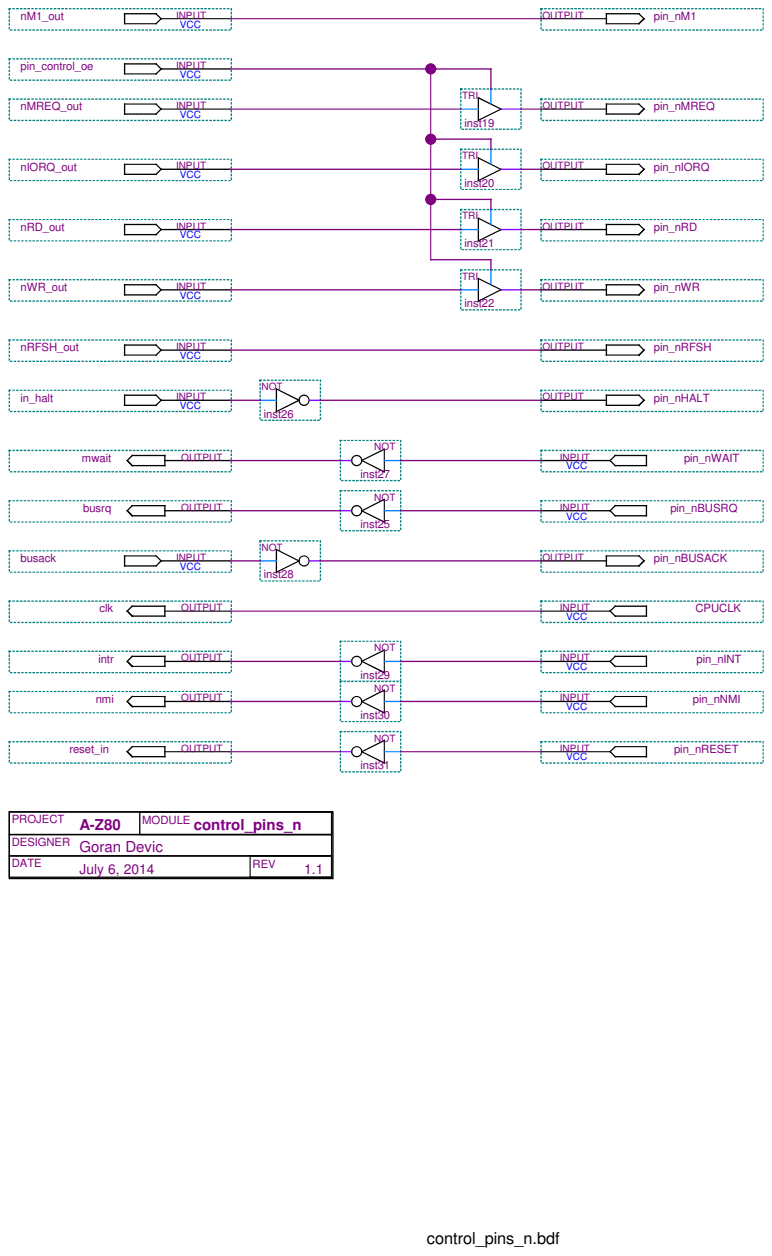
[picture p86: page 1]
control_pins_n.bdf; VCC; busack; INPUT; CPUCLK; pin_control_oe; in_halt; pin_nWAIT; pin_nBUSRQ; pin_nINT; pin_nNMI; pin_nRESET; nM1_out; nRFSH_out; nRD_out; nWR_out; nIORQ_out; nMREQ_out; nmi; OUTPUT; busrq; clk; intr; mwait; reset_in; pin_nM1; pin_nMREQ; pin_nIORQ; pin_nRD; pin_nWR; pin_nRFSH; pin_nHALT; pin_nBUSACK; TRI; inst19; inst20; inst21; inst22; NOT; inst26; inst28; inst25; inst29 NOT; inst30; inst31; inst27; PROJECT; MODULE control_pins_n; DATE; July 6, 2014; REV

DESIGNER Goran Devic
