allisonmb/game-gear/A-Z80/docs/pdf/decode_state.pdf

## IX and IY state flags

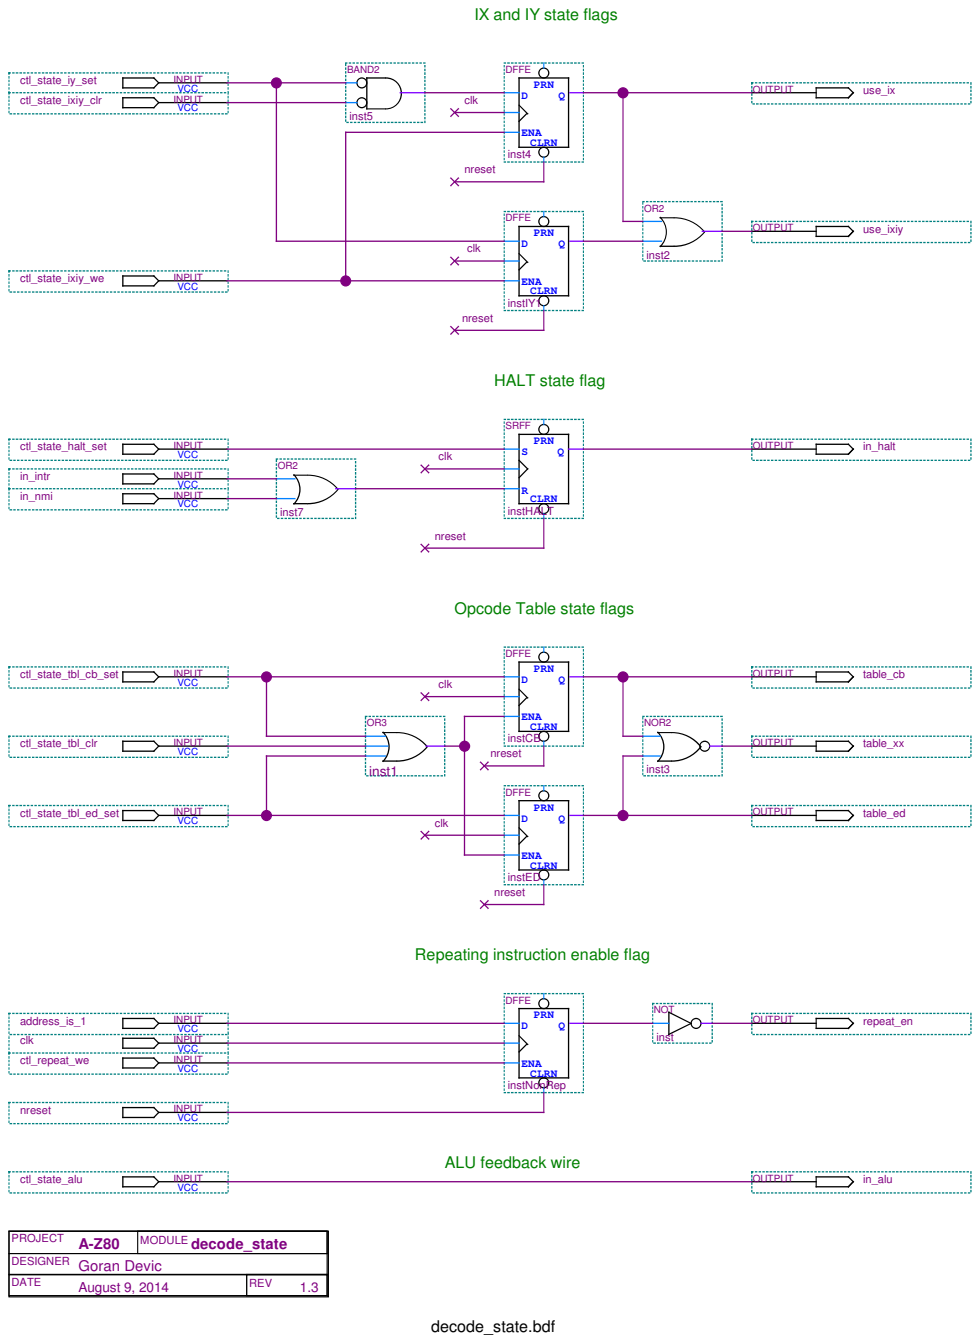
[picture p87: page 1]
decode_state.bdf; clk; nreset; VCC; ctl_state_iy_set; INPUT; ctl_state_ixiy_clr; ctl_state_ixiy_we; ctl_state_halt_set; ctl_state_tbl_clr; ctl_state_tbl_ed_set; ctl_state_tbl_cb_set; ctl_state_alu; address_is_1; ctl_repeat_we; in_intr; in_nmi; OUTPUT; in_halt; table_cb; table_ed; table_xx; use_ix; use_ixiy; in_alu; repeat_en; inst2; inst1; NOR2; inst3; BAND2; inst5; NOT; inst; PRN; CLRN; SRFF; instHALT; inst7; ENA; DFFE; inst4; instIY1; instCB; instED; instNonRep; DATE; August 9, 2014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

HALT state flag

Opcode Table state flags

Repeating instruction enable flag

ALU feedback wire

DESIGNER Goran Devic
