allisonmb/game-gear/A-Z80/docs/pdf/inc_dec.pdf

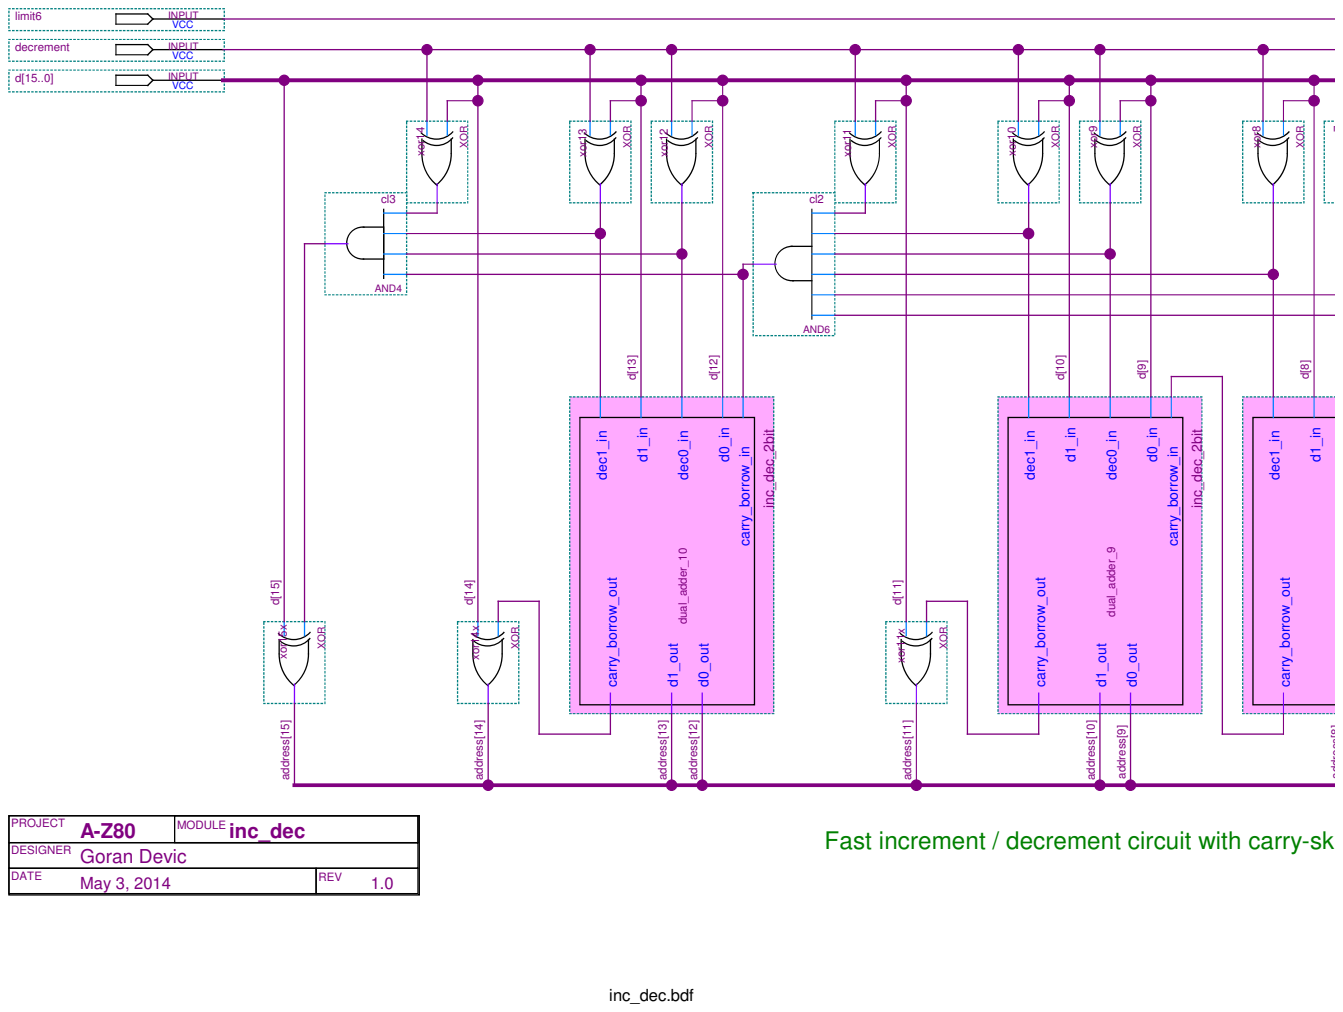
[picture p88: page 1]
inc_dec.bdf; address[15]; address[14]; address[13]; address[12]; address[11]; address[10]; address[9]; address[8]; VCC limit6; INPUT; VCC decrement; VCC d[15..0]; XOR; xor10; xor9; xor8; xor7; xor11x; xor11; AND6; xor12; xor13; xor14x; xor14; AND4; xor15x; dec1_in; carry_borrow_out; carry_borrow_in; dec0_in; d1_out; d0_out; inc_dec_2bit; dual_adder_9; dual_adder_10; DATE; May 3, 2014; MODULE inc_dec PROJECT; REV

DESIGNER Goran Devic

Fast increment / decrement circuit with carry-ski

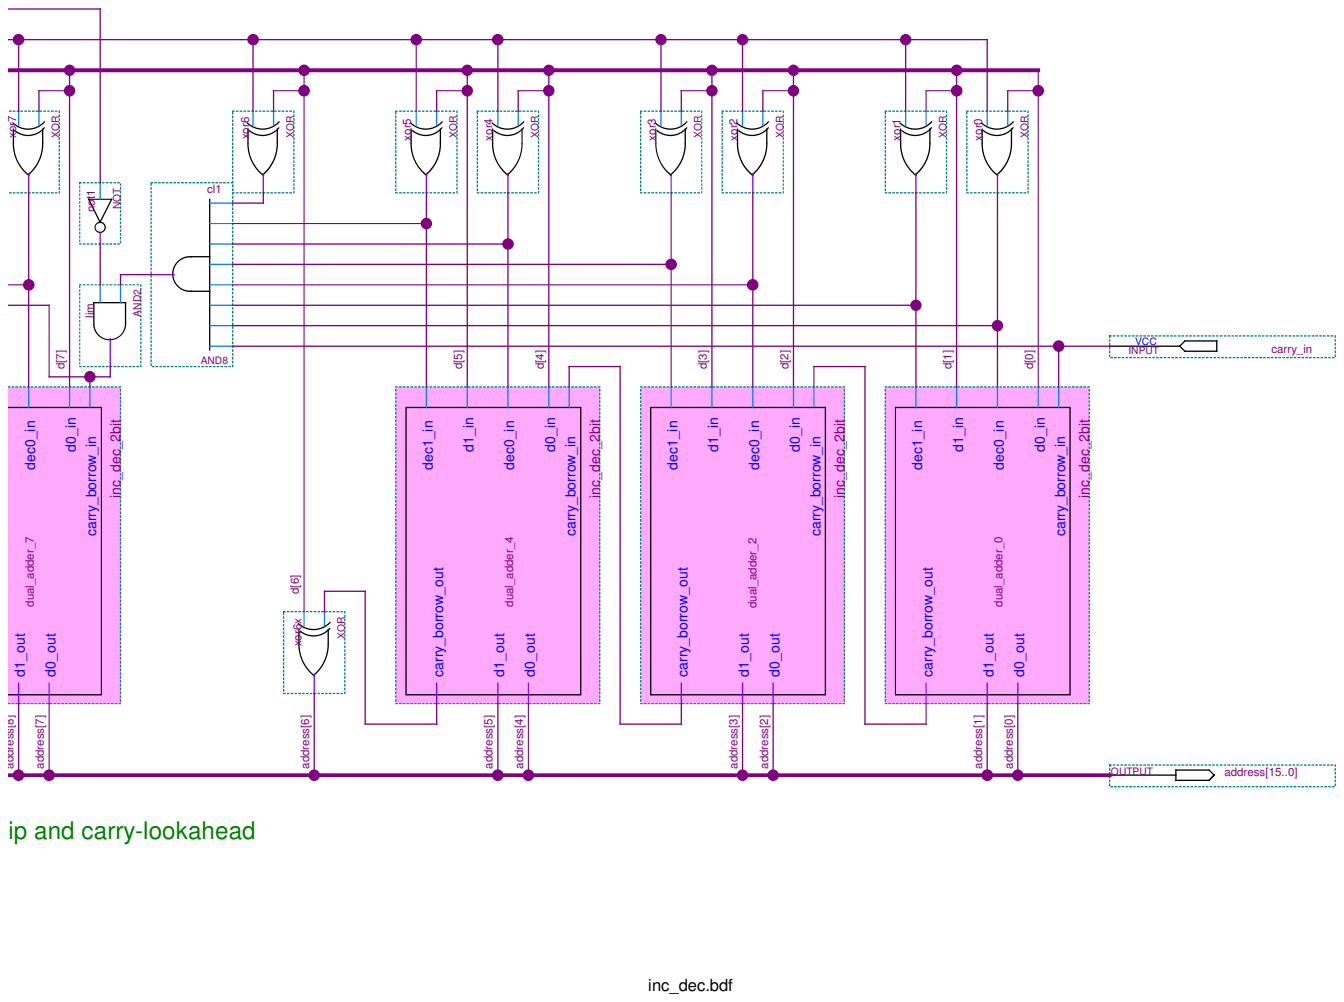
[picture p89: page 2]
inc_dec.bdf; address[8]; address[7]; address[6]; address[5]; address[4]; address[3]; address[2]; address[1]; address[0]; VCC; INPUT; carry_in; OUTPUT; address[15..0]; xor5; XOR; xor4; xor3; xor2; xor1; xor0; xor6x; xor6; AND8; lim; AND2; xor7; not1; NOT; carry_borrow_in; dec1_in; dec0_in; carry_borrow_out; d1_out; d0_out; inc_dec_2bit; dual_adder_0; dual_adder_2; dual_adder_4; dual_adder_7

and carry-lookahead
