allisonmb/game-gear/A-Z80/docs/pdf/pin_control.pdf

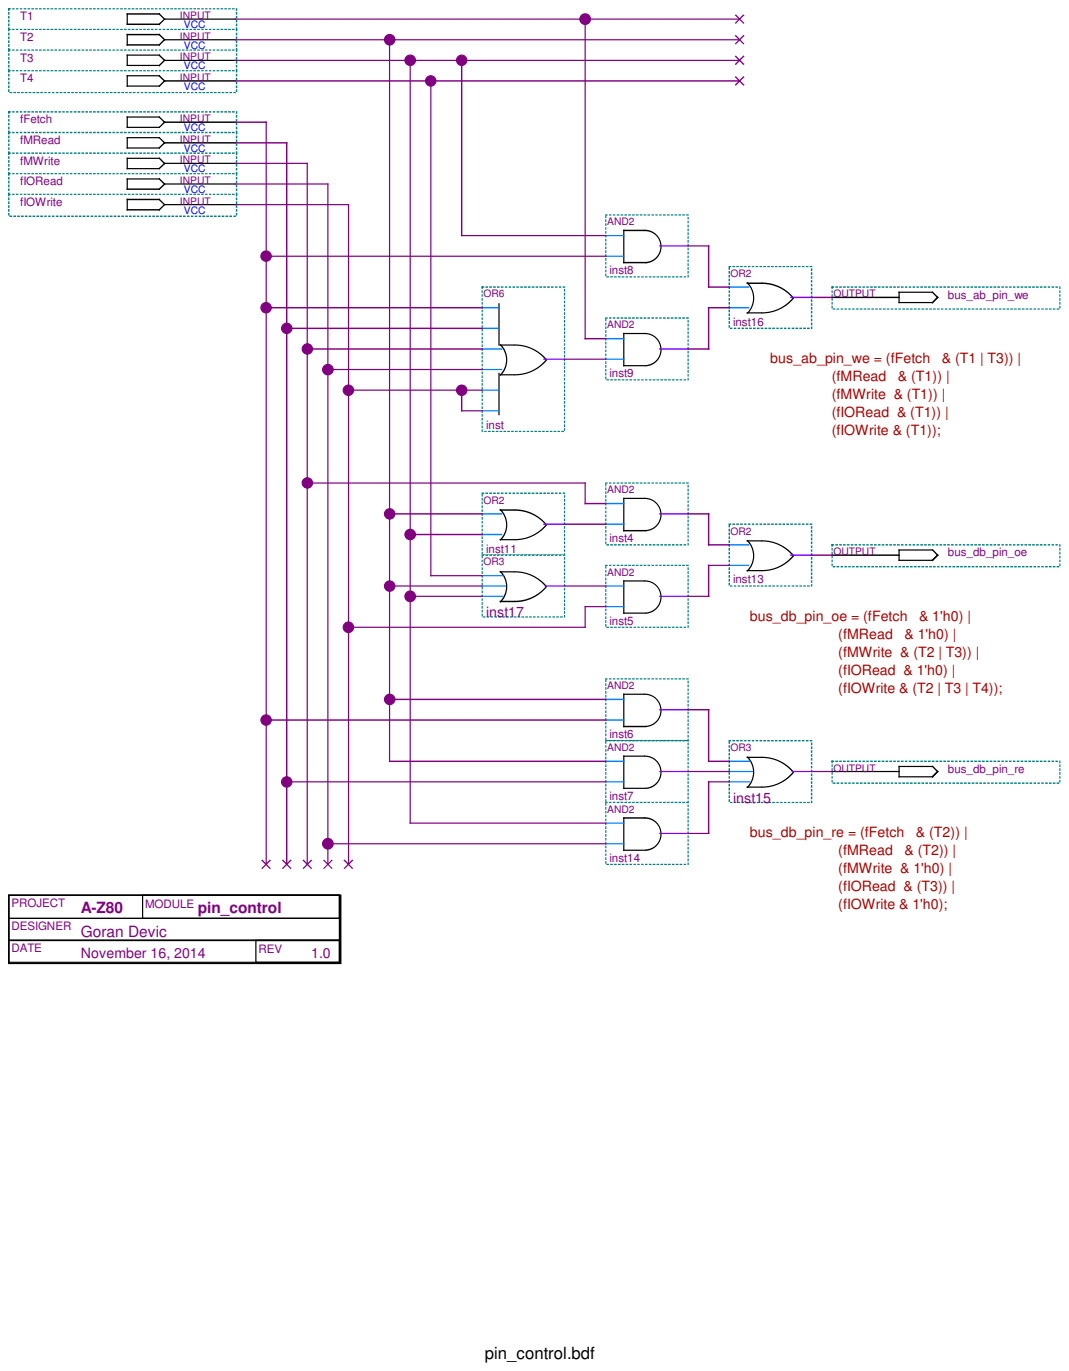
[picture p90: page 1]
pin_control.bdf; bus_ab_pin_we = (fFetch & (T1 | T3)) | (fMRead & (T1)) | (fMWrite & (T1)) | (fIORead & (T1)) | (fIOWrite & (T1));; bus_db_pin_oe = (fFetch & 1'h0) | (fMRead & 1'h0) | (fMWrite & (T2 | T3)) | (fIORead & 1'h0) | (fIOWrite & (T2 | T3 | T4));; bus_db_pin_re = (fFetch & (T2)) | (fMRead & (T2)) | (fMWrite & 1'h0) | (fIORead & (T3)) | (fIOWrite & 1'h0);; VCC; fFetch; INPUT; fMRead; fMWrite; fIORead; fIOWrite; OUTPUT; bus_ab_pin_we; bus_db_pin_oe; bus_db_pin_re; inst11; AND2; inst4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

DESIGNER Goran Devic
