allisonmb/game-gear/A-Z80/docs/pdf/reg_control.pdf

## General Purpose registers control

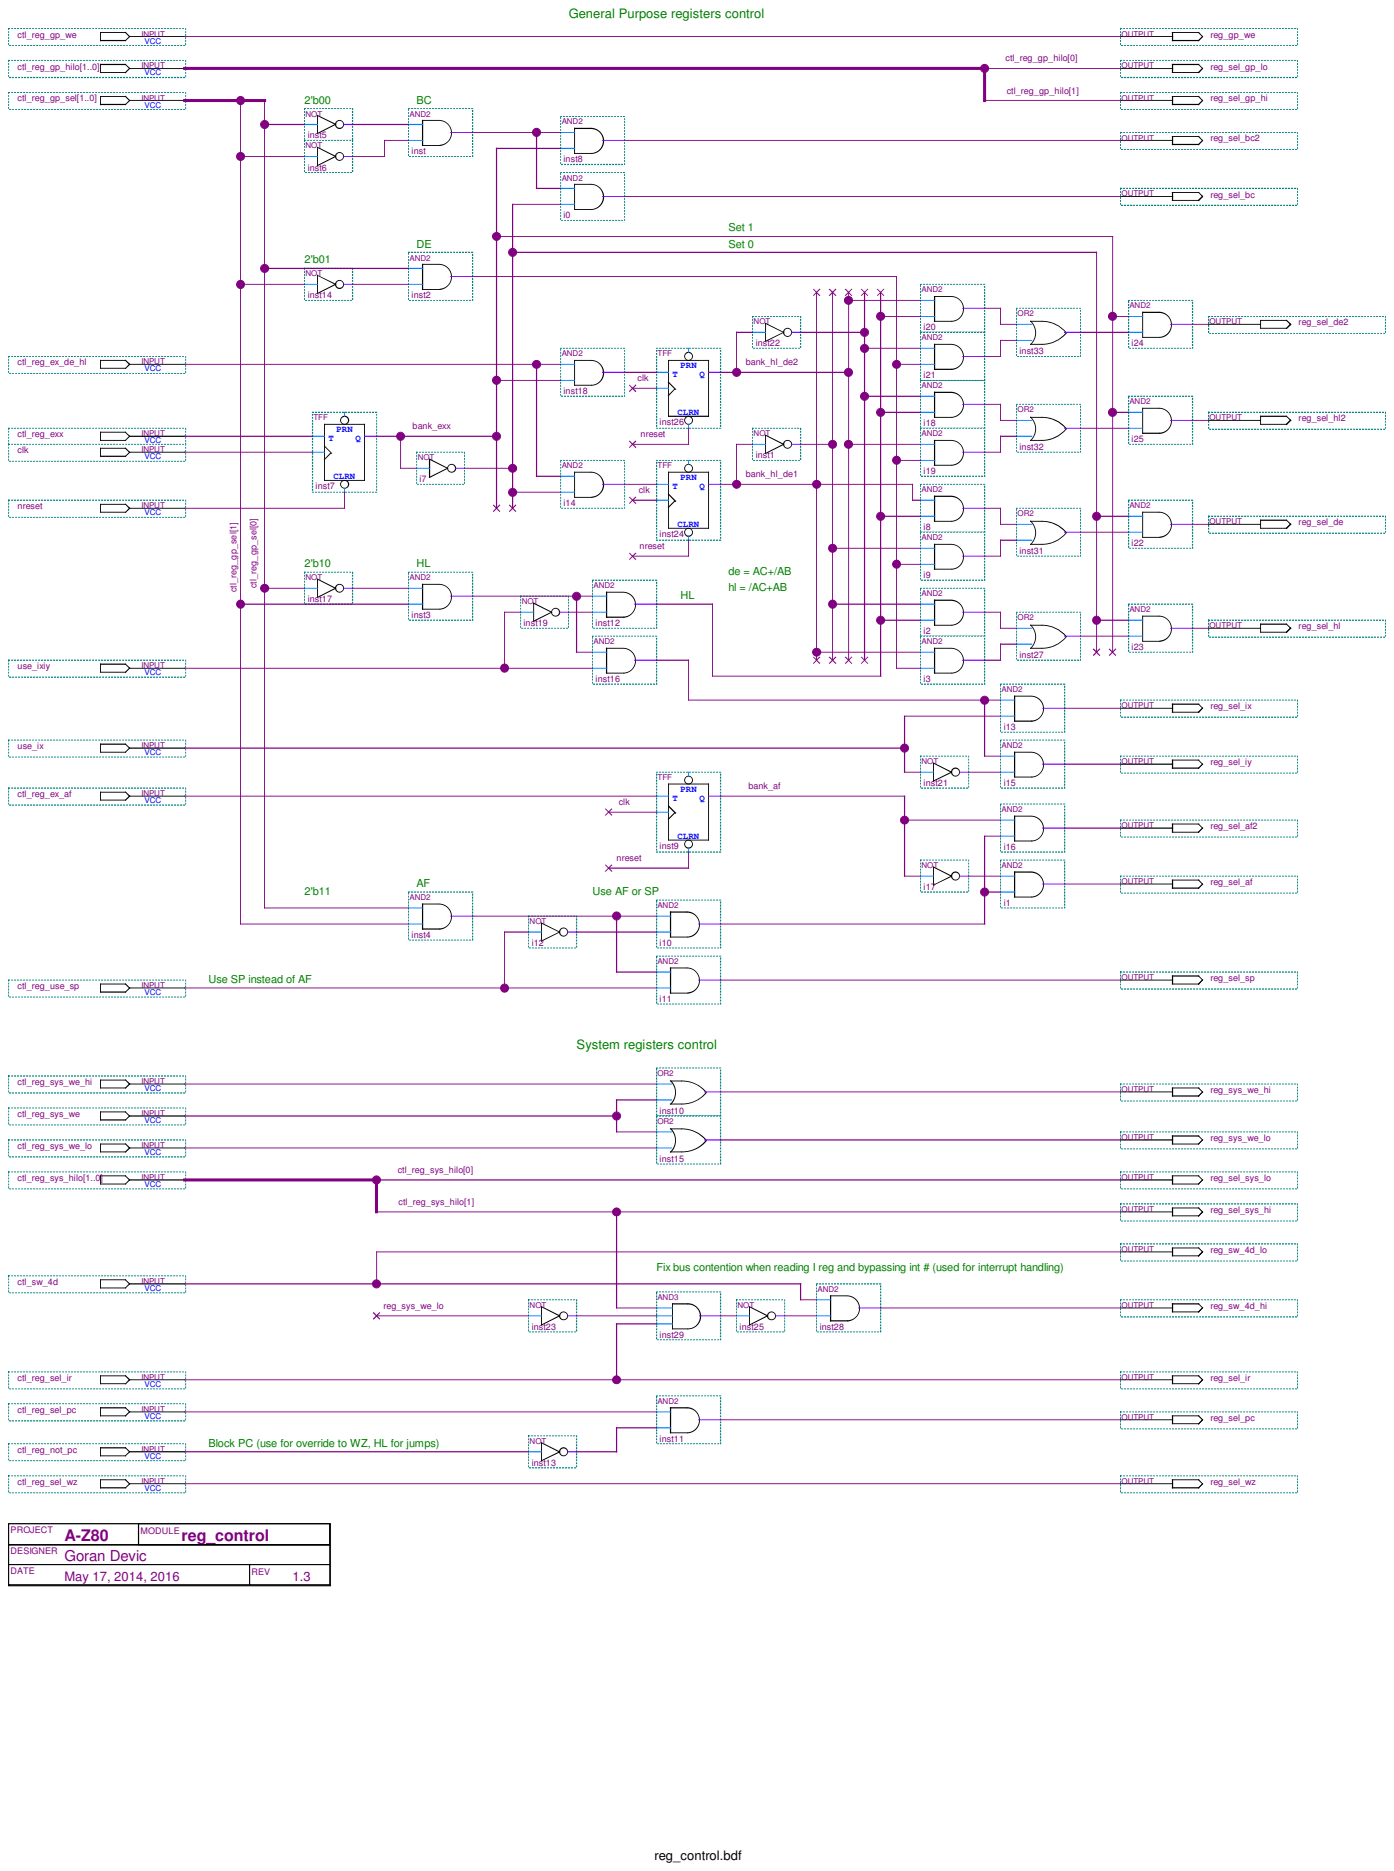
[picture p91: page 1]
reg_control.bdf; ctl_reg_gp_sel[1]; ctl_reg_gp_sel[0]; ctl_reg_gp_hilo[1]; ctl_reg_gp_hilo[0]; bank_exx; nreset; clk; bank_hl_de2; bank_hl_de1; bank_af; ctl_reg_sys_hilo[0]; ctl_reg_sys_hilo[1]; reg_sys_we_lo; Use AF or SP; Set 0; Set 1; VCC; ctl_reg_gp_sel[1..0]; INPUT; ctl_reg_sys_hilo[1..0]; ctl_reg_exx; ctl_reg_ex_af; ctl_reg_ex_de_hl; ctl_reg_use_sp; VCC ctl_reg_gp_hilo[1..0]; VCC ctl_reg_sel_pc; ctl_reg_sel_ir; ctl_reg_sel_wz; ctl_reg_gp_we; ctl_reg_not_pc; VCC use_ixiy; use_ix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

Use SP instead of AF

System registers control

Fix bus contention when reading I reg and bypassing int # (used for interrupt handling)

Block PC (use for override to WZ, HL for jumps)

DESIGNER Goran Devic
