allisonmb/game-gear/A-Z80/docs/pdf/reg_file.pdf

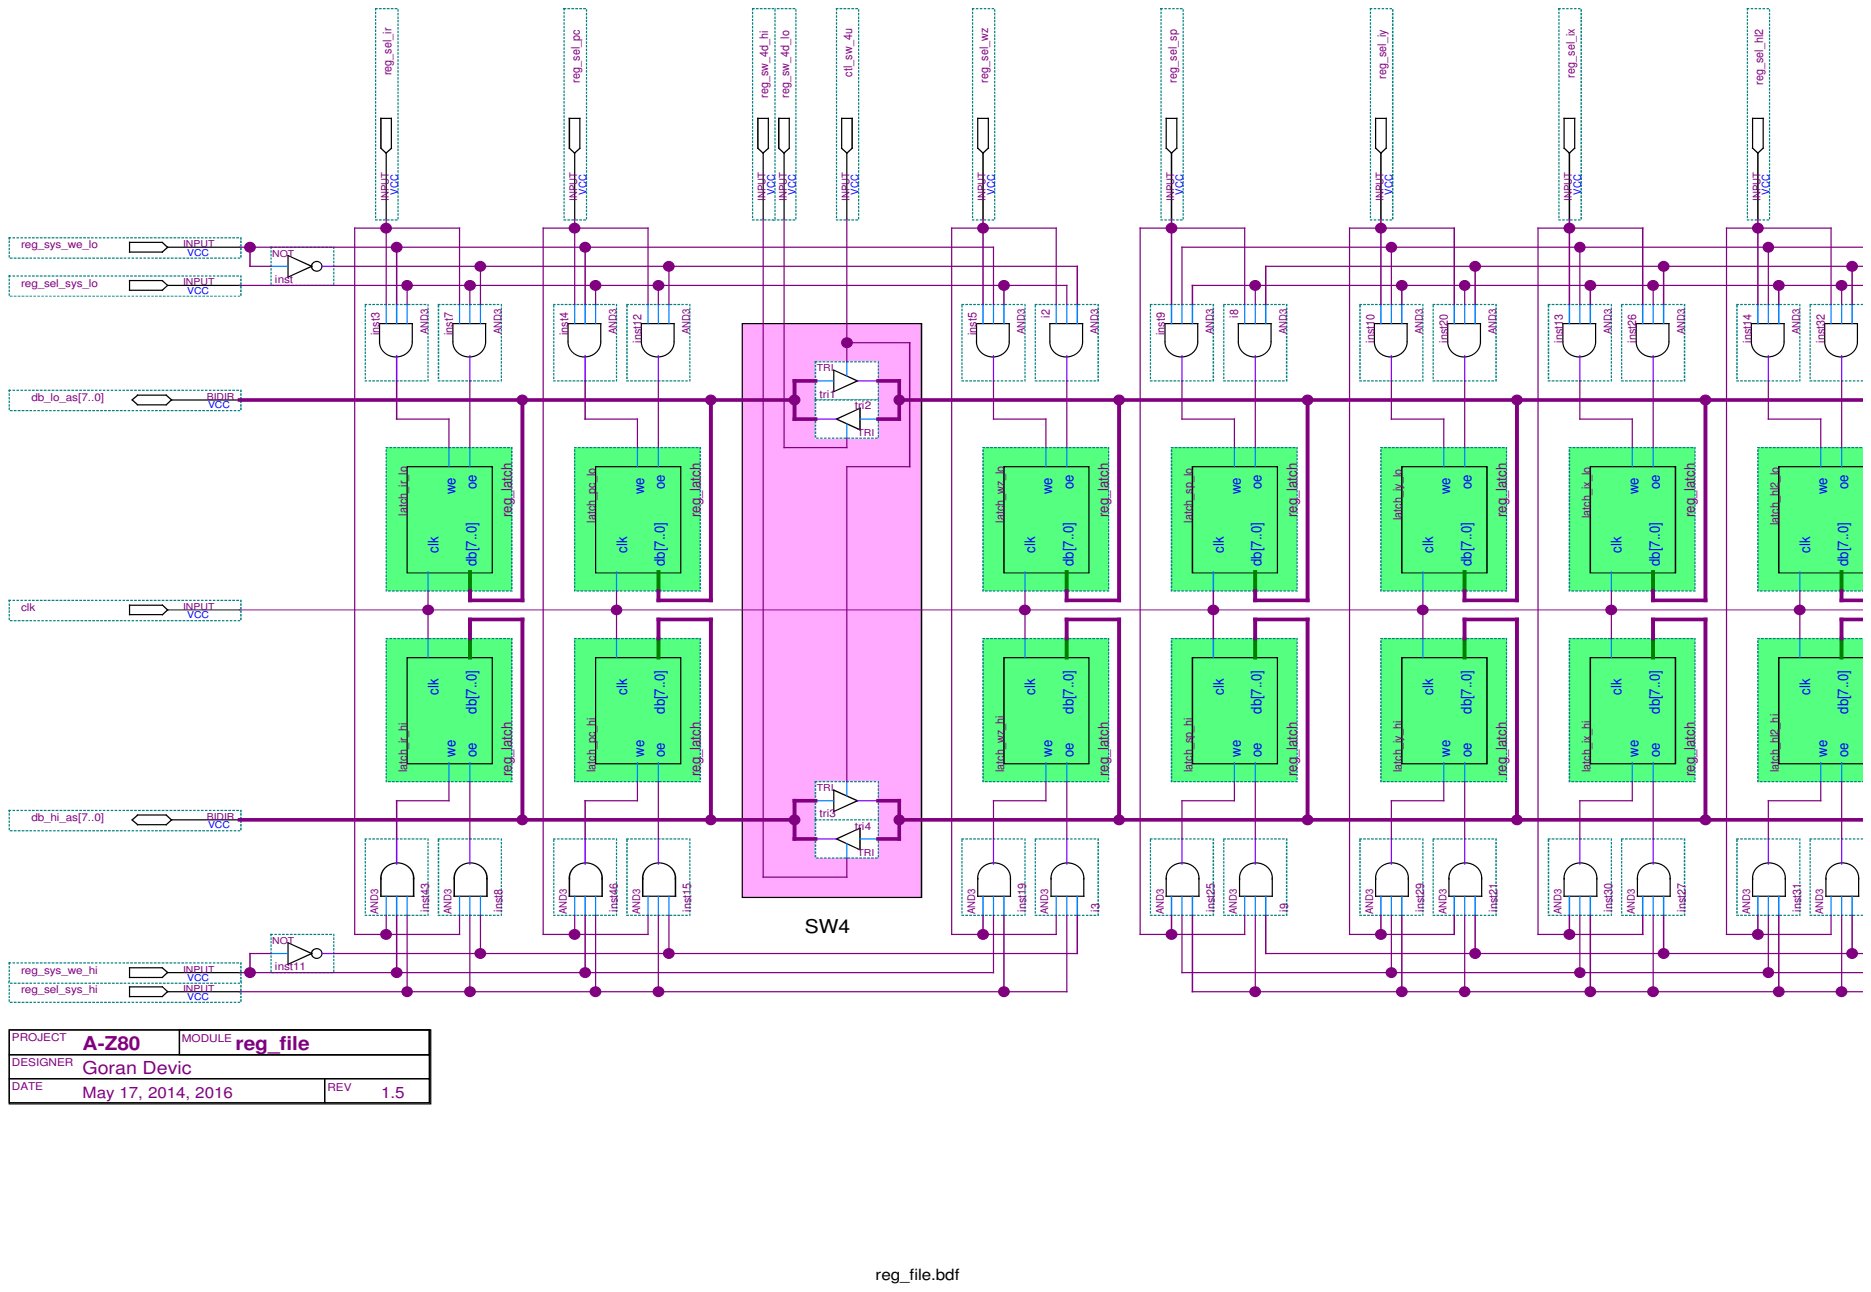
[picture p92: page 1]
reg_file.bdf; VCC reg_sel_sys_lo; INPUT; VCC reg_sel_sys_hi; VCC; reg_sel_ir INPUT; reg_sel_pc INPUT; ctl_sw_4u INPUT; reg_sel_wz INPUT; reg_sel_sp INPUT; reg_sel_iy INPUT; reg_sel_ix INPUT; reg_sel_hl2 INPUT; VCC reg_sys_we_lo; VCC reg_sys_we_hi; VCC clk; reg_sw_4d_lo INPUT; reg_sw_4d_hi; VCC db_lo_as[7..0]; BIDIR; VCC db_hi_as[7..0]; inst7; AND3; inst8; inst12 AND3; inst15; inst20 AND3; inst21; inst26 AND3; inst27; inst32 AND3; i2 AND3; i8 AND3; clk; latch_iy_lo; reg_latch; latch_iy_hi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

DESIGNER Goran Devic

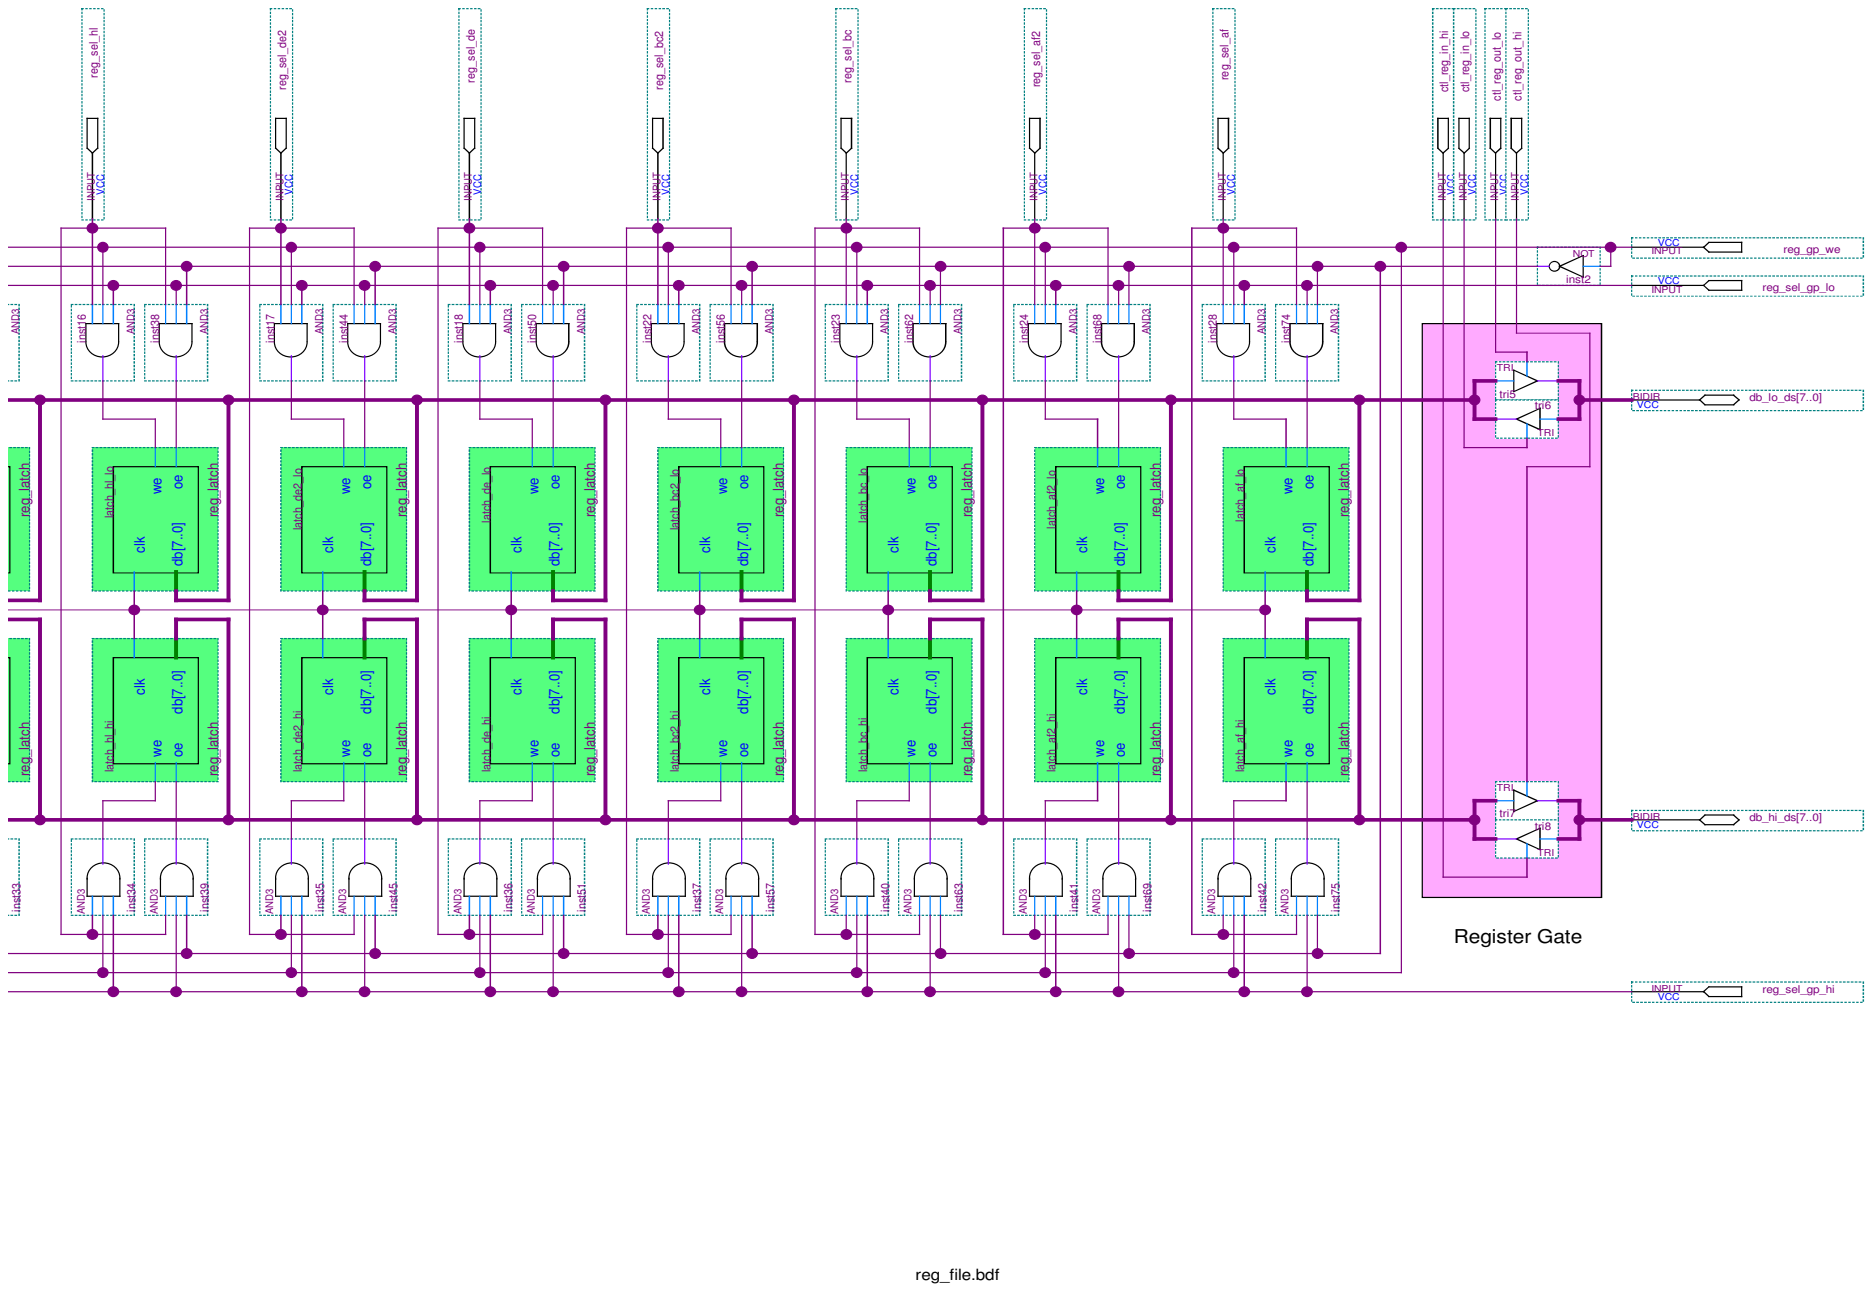
[picture p93: page 2]
reg_file.bdf; Register Gate; VCC; INPUT; reg_sel_gp_lo; reg_sel_gp_hi; reg_sel_hl; reg_sel_de2 INPUT; reg_sel_de INPUT; reg_sel_bc2 INPUT; reg_sel_bc INPUT; reg_sel_af2 INPUT; reg_sel_af; reg_gp_we; ctl_reg_in_hi INPUT; ctl_reg_in_lo INPUT; ctl_reg_out_lo INPUT; ctl_reg_out_hi; BIDIR; AND3 inst33; AND3; inst38 AND3; inst39; inst44 AND3; inst45; inst50 AND3; inst51; inst56 AND3; inst57; inst62 AND3; inst63; inst68 AND3; inst69; inst74 AND3; inst75; reg_latch; clk; latch_hl_lo; latch_hl_hi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
