allisonmb/game-gear/romDev/subOutput/assets.asm

;--------------------------------------------------------
; File Created by SDCC : free open source ISO C Compiler 
; Version 4.4.0 #14620 (MINGW64)
;--------------------------------------------------------
	.module assets
	.optsdcc -mz80
	
;--------------------------------------------------------
; Public variables in this module
;--------------------------------------------------------
	.globl _TestingComplete_stmcompr
	.globl _TestingComplete_psgcompr
	.globl _TestingComplete_bin
	.globl _Testing1_stmcompr
	.globl _Testing1_psgcompr
	.globl _Testing1_bin
	.globl _TestFailed_psgcompr
	.globl _TestFailed_bin
	.globl _TestFailed__stmcompr
	.globl _Spritesheet_psgcompr
	.globl _Spritesheet_bin
	.globl _Numbers_psgcompr
	.globl _Numbers_bin
	.globl _Nole_psgcompr
	.globl _Nole_bin
	.globl _HelloWorldTiles_psgcompr
	.globl _HelloWorldTilemap_stmcompr
	.globl _HelloWorldPalette_bin
	.globl _gator_psgcompr
	.globl _gator_bin
	.globl _DemoBG_stmcompr
	.globl _DemoBG_psgcompr
	.globl _DemoBG_bin
	.globl _BallTileMap_bin
	.globl _BallNoChecks_psgcompr
	.globl _BallNew_psgcompr
	.globl _BallMirror_psgcompr
	.globl _BallEight_psgcompr
	.globl _Ball_stmcompr
	.globl _Ball_psgcompr
	.globl _Ball_bin
;--------------------------------------------------------
; special function registers
;--------------------------------------------------------
;--------------------------------------------------------
; ram data
;--------------------------------------------------------
	.area _DATA
;--------------------------------------------------------
; ram data
;--------------------------------------------------------
	.area _INITIALIZED
;--------------------------------------------------------
; absolute external ram data
;--------------------------------------------------------
	.area _DABS (ABS)
;--------------------------------------------------------
; global & static initialisations
;--------------------------------------------------------
	.area _HOME
	.area _GSINIT
	.area _GSFINAL
	.area _GSINIT
;--------------------------------------------------------
; Home
;--------------------------------------------------------
	.area _HOME
	.area _HOME
;--------------------------------------------------------
; code
;--------------------------------------------------------
	.area _CODE
	.area _CODE
_Ball_bin:
	.db #0x00	; 0
	.db #0x00	; 0
	.db #0x04	; 4
	.db #0x00	; 0
	.db #0x04	; 4
	.db #0x00	; 0
	.db #0x06	; 6
	.db #0x00	; 0
	.db #0x07	; 7
	.db #0x00	; 0
	.db #0x18	; 24
	.db #0x01	; 1
	.db #0x18	; 24
	.db #0x01	; 1
	.db #0x1a	; 26
	.db #0x01	; 1
	.db #0x1a	; 26
	.db #0x01	; 1
	.db #0x1a	; 26
	.db #0x01	; 1
	.db #0x1c	; 28
	.db #0x02	; 2
	.db #0x2b	; 43
	.db #0x02	; 2
	.db #0x2c	; 44
	.db #0x02	; 2
	.db #0x2d	; 45
	.db #0x02	; 2
	.db #0x2d	; 45
	.db #0x02	; 2
	.db #0x2d	; 45
	.db #0x02	; 2
_Ball_psgcompr:
	.db #0x0d	; 13
	.db #0x00	; 0
	.db #0xea	; 234
	.db #0x00	; 0
	.db #0x00	; 0
	.db #0x01	; 1
	.db #0x03	; 3
	.db #0x0b	; 11
	.db #0x07	; 7
	.db #0x1f	; 31
	.db #0x3f	; 63
	.db #0x20	; 32
	.db #0xd5	; 213
	.db #0x03	; 3
	.db #0x03	; 3
	.db #0x3f	; 63
	.db #0x20	; 32
	.db #0xe1	; 225
	.db #0x05	; 5
	.db #0x0f	; 15
	.db #0x1f	; 31
	.db #0x0f	; 15
	.db #0x20	; 32
	.db #0xd2	; 210
	.db #0x00	; 0
	.db #0x07	; 7
	.db #0x0f	; 15
	.db #0x1f	; 31
	.db #0xaa	; 170
	.db #0x1f	; 31
	.db #0xff	; 255
	.db #0x2a	; 42
	.db #0xbf	; 191
	.db #0x7f	; 127
	.db #0x3f	; 63
	.db #0xff	; 255
	.db #0x15	; 21
	.db #0x9f	; 159
	.db #0x3f	; 63
	.db #0xff	; 255
	.db #0x13	; 19
	.db #0x3f	; 63
	.db #0x3f	; 63
	.db #0xff	; 255
	.db #0x0f	; 15
	.db #0x7f	; 127
	.db #0xaa	; 170
	.db #0x1f	; 31
	.db #0xff	; 255
	.db #0x54	; 84	'T'
	.db #0xfd	; 253
	.db #0xfe	; 254
	.db #0x3f	; 63
	.db #0xff	; 255
	.db #0xa8	; 168
	.db #0xf9	; 249
	.db #0x3f	; 63
	.db #0xff	; 255
	.db #0xc8	; 200
	.db #0xfc	; 252
	.db #0x3f	; 63
	.db #0xff	; 255
	.db #0xf0	; 240
	.db #0xfe	; 254
	.db #0xea	; 234
	.db #0x00	; 0
	.db #0x00	; 0
	.db #0x80	; 128
	.db #0xc0	; 192
	.db #0xd0	; 208
	.db #0xe0	; 224
	.db #0xf8	; 248
	.db #0xfc	; 252
	.db #0x20	; 32
	.db #0xd5	; 213
	.db #0xc0	; 192
	.db #0xc0	; 192
	.db #0xfc	; 252
	.db #0x20	; 32
	.db #0xe1	; 225
	.db #0xa0	; 160
	.db #0xf0	; 240
	.db #0xf8	; 248
	.db #0xf0	; 240
	.db #0x20	; 32
	.db #0xd2	; 210
	.db #0x00	; 0
	.db #0xe0	; 224
	.db #0xf0	; 240
	.db #0xf8	; 248
	.db #0xaa	; 170
	.db #0x15	; 21
	.db #0x7f	; 127
	.db #0x5f	; 95
	.db #0x3f	; 63
	.db #0xff	; 255
	.db #0xff	; 255
	.db #0xff	; 255
	.db #0x8a	; 138
	.db #0x7f	; 127
	.db #0x3f	; 63
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
	.db #0x3c	; 60
	.db #0x20	; 32
	.db #0x47	; 71	'G'
	.db #0xff	; 255
	.db #0xc6	; 198
	.db #0xf6	; 246
	.db #0x7e	; 126
	.db #0x20	; 32
	.db #0x47	; 71	'G'
	.db #0x81	; 129
	.db #0xc2	; 194
	.db #0x62	; 98	'b'
	.db #0x78	; 120	'x'
	.db #0xa8	; 168
	.db #0x07	; 7
	.db #0x00	; 0
	.db #0x3e	; 62
	.db #0x07	; 7
	.db #0x43	; 67	'C'
	.db #0x77	; 119	'w'
	.db #0x3e	; 62
	.db #0x07	; 7
	.db #0x00	; 0
	.db #0x1f	; 31
	.db #0x03	; 3
	.db #0x61	; 97	'a'
	.db #0x6b	; 107	'k'
	.db #0x3f	; 63
	.db #0x07	; 7
	.db #0x00	; 0
	.db #0x0f	; 15
	.db #0x01	; 1
	.db #0x21	; 33
	.db #0x21	; 33
	.db #0x1c	; 28
	.db #0xa8	; 168
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
